Exerqtor/Voron/Firmware/rrf-macros/README.md

# Firmware Configurations

Firmware Configurations for Voron 3D printers, separated by firmware.
Remember to update this README when uploading new firmware configurations!

## Table structure

Update the following table with the information about your mod:
- Your name
- A link to your sub-folder
- A short description of your firmware config
- The printer compatibility. Use `:heavy_check_mark:` for :heavy_check_mark:,`:x:` for :x: and `:grey_question:` for :grey_question:

like so:
`
| Creator | [Config Title](link) | Description | :x: | :x: | :x: | :x: |`

---
## RepRapFirmware

| Creator | Config title | Description | V0 | V1.8 | V2.4 | VSW | VT |
| --- | --- | --- | --- | --- | --- | --- | --- |
| Exerqtor | [Adaptive Purge](./adaptive_purge/) | Purges a Voron logo right next to the print | - | - | - | - | - |
|  | [Nozzle Scrub](./nozzle_scrub/) | Script to clean your nozzle on a brush| - | - | - | - | - |
|  | [TAP Temp Control](./tap_temp_control/) | Script to make sure the nozzle is bellow 150°C when probing| - | - | - | - | - |
|  | [M48 Probe Repeatability Test](./m48_probe_repeatability_test/) | Script to test your Z probes repeatability| - | - | - | - | - |
|  | [StealthBurner LED's](./sb_leds/) | NanoLED controll for stealthburner toolhead| - | - | - | - | - |
