Exerqtor/Voron/Mods/fume_pack/pics/fancut1.png

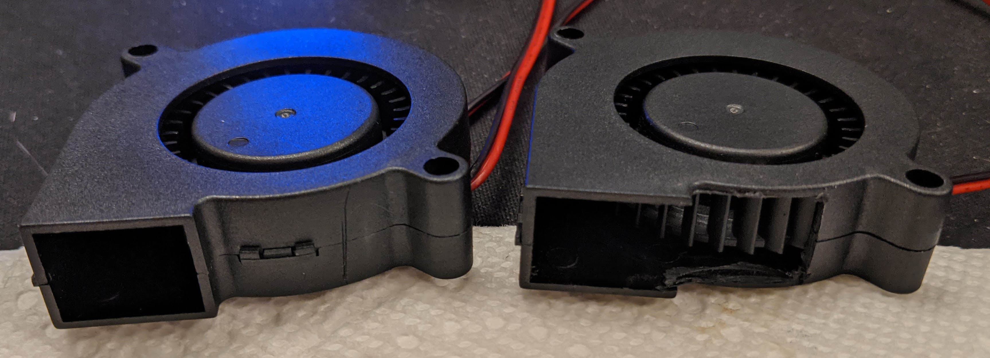
Mods/fume_pack/pics/fancut1.png
