Exerqtor/Voron/Mods/halo_hex/pics/2C-1.PNG

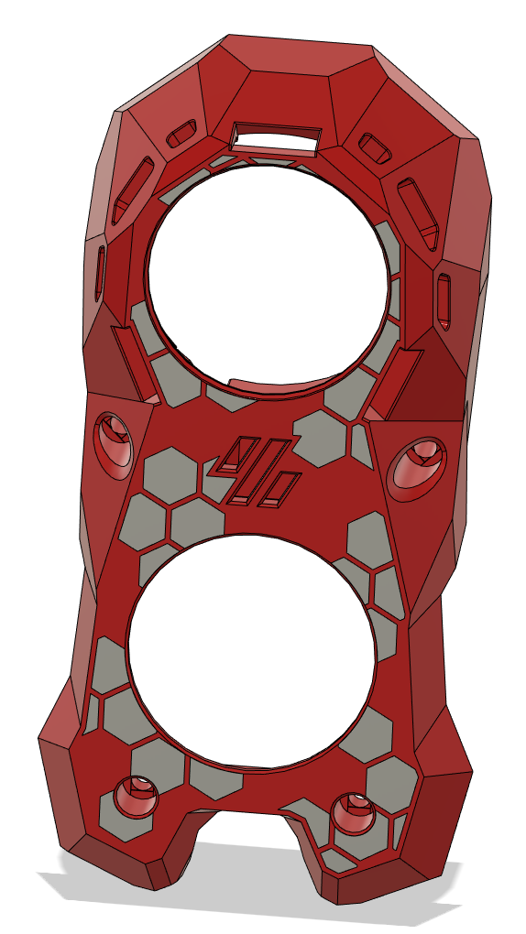
Mods/halo_hex/pics/2C-1.PNG
