Exerqtor/Voron/Mods/halo_hex/pics/3C-1.PNG

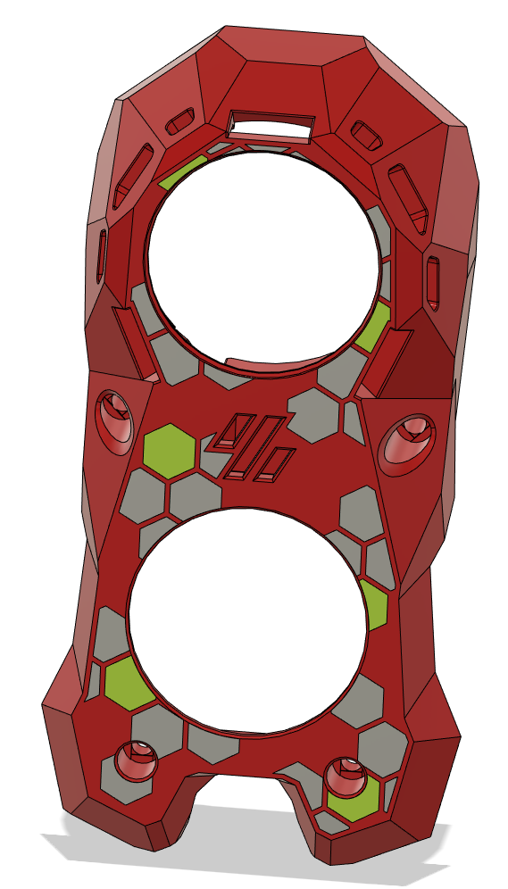
Mods/halo_hex/pics/3C-1.PNG
