Exerqtor/Voron/Mods/knomi_hex/pics/1.png

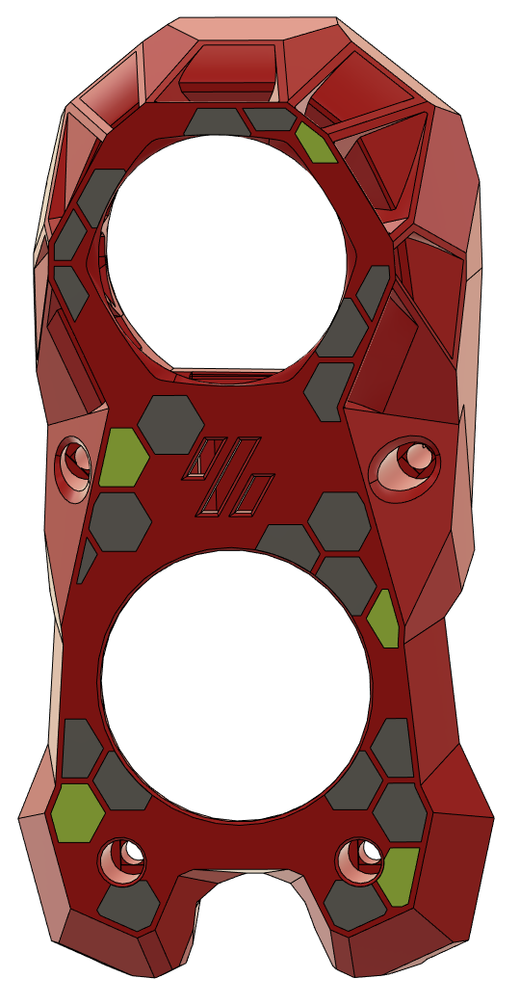
Mods/knomi_hex/pics/1.png
