Exerqtor/Voron/Mods/vt_4mm_extra_y/pics/3.PNG

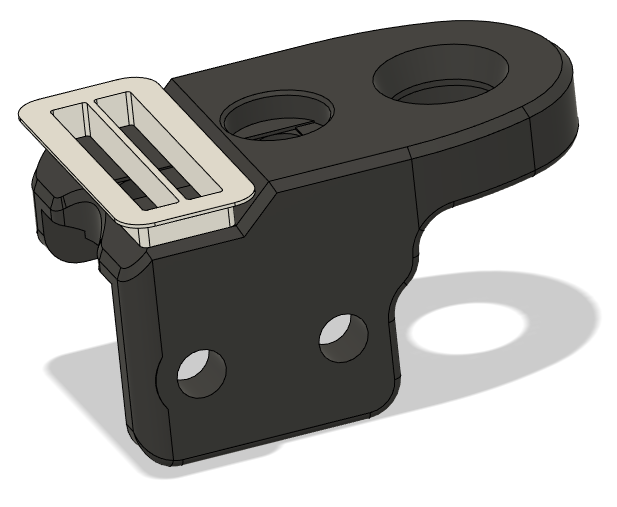
Mods/vt_4mm_extra_y/pics/3.PNG
