Exerqtor/Voron/Mods/knomi_hex/midlertidig!/NO-KNOMI-h.stl

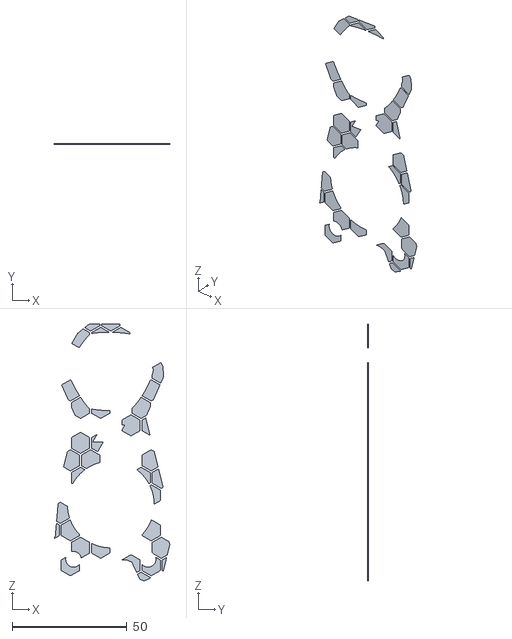
[picture p104: CAD file, 2024-03-30]
Mods/knomi_hex/midlertidig!/NO-KNOMI-h.stl
50.5 x 0.2 x 112.0
