Exerqtor/Voron/Mods/knomi_hex/STL/3_colors/KNOMI-HEX_hex-2.stl

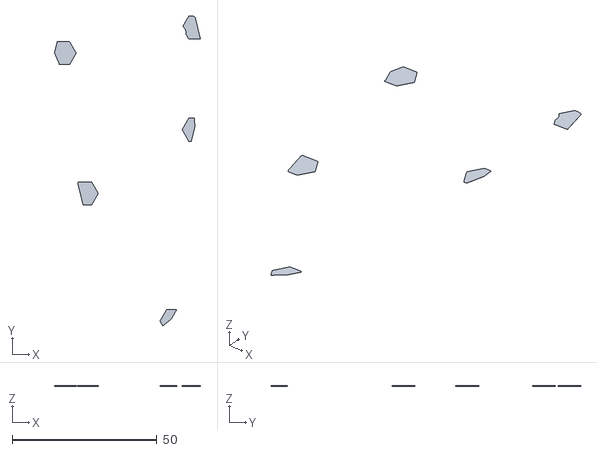
[picture p105: CAD file, 2024-03-30]
Mods/knomi_hex/STL/3_colors/KNOMI-HEX_hex-2.stl
50.4 x 106.9 x 0.2
