Exerqtor/Voron/Mods/lgx-lite_filament_sensor/CAD/LGX-lite_filament_sensor.step

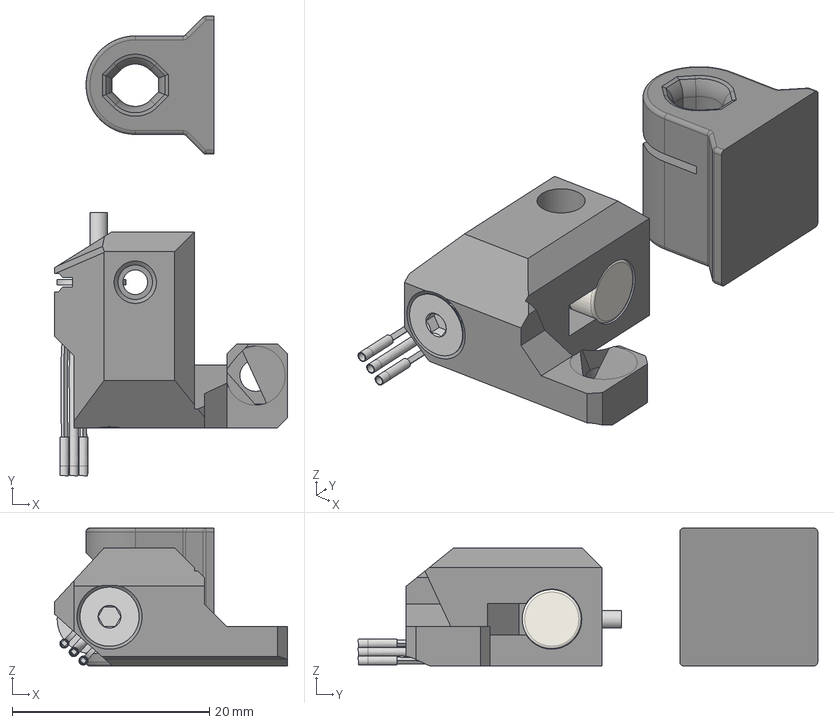
[picture p106: CAD file, 2025-02-17]
Mods/lgx-lite_filament_sensor/CAD/LGX-lite_filament_sensor.step
23.6 x 46.6 x 14.0 mm
Magnet6x3 v1
AH3364Q-P-B v4
ferromagnetic washer
92125A126_NO THREADS_18-8 Stainless Steel Hex Drive Flat Head Screw
Filament stump
PTFE cut jig
