Exerqtor/Voron/Mods/lgx-lite_filament_sensor/STL/PTFE_cut_jig.stl

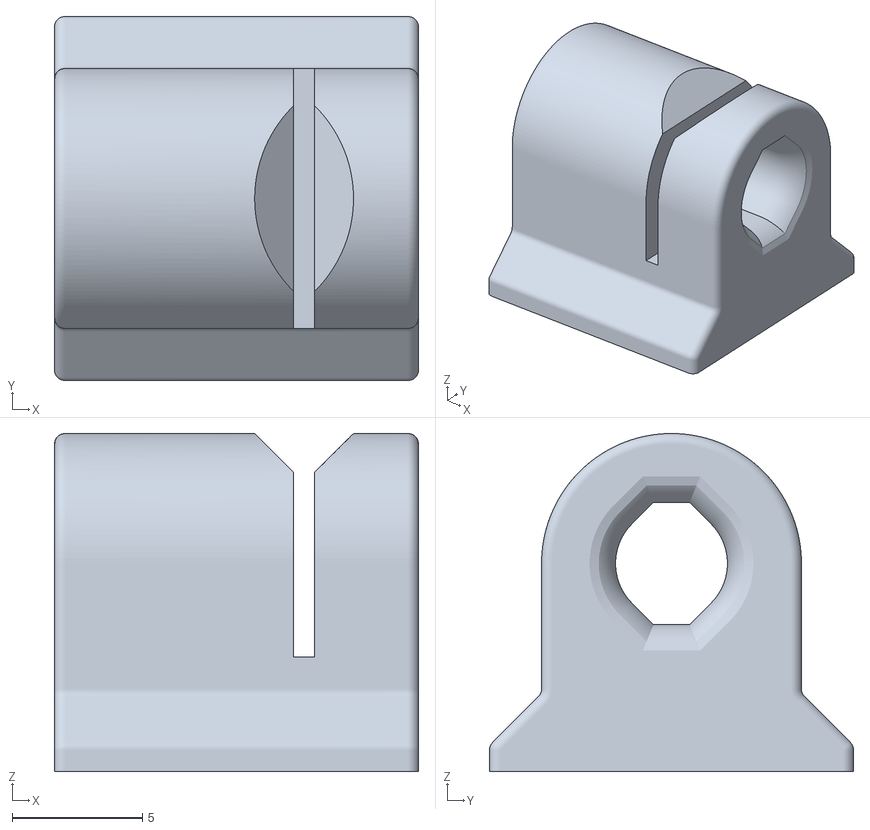
[picture p107: CAD file, 2025-02-17]
Mods/lgx-lite_filament_sensor/STL/PTFE_cut_jig.stl
14.0 x 14.0 x 13.0
