Exerqtor/Voron/Mods/mesh_skirts/Middle_Fan_Support/CAD/Middle_Fan_Support.step

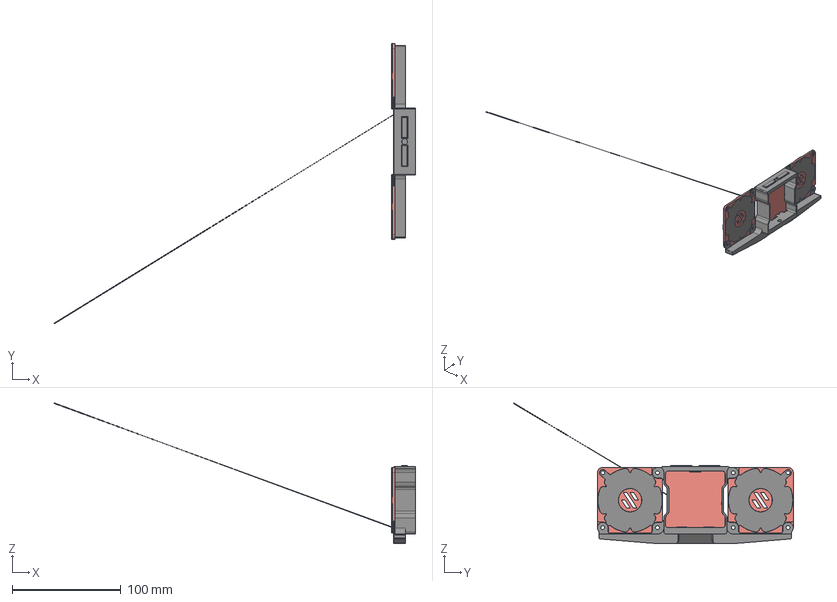
[picture p108: CAD file, 2023-04-12]
Mods/mesh_skirts/Middle_Fan_Support/CAD/Middle_Fan_Support.step
331.8 x 257.0 x 129.1 mm
Middle Fan Support
Fan Grill B
Fan Grill A
