Exerqtor/Voron/Mods/mesh_skirts/Middle_Fan_Support/STL/side_fan_support_x2.stl

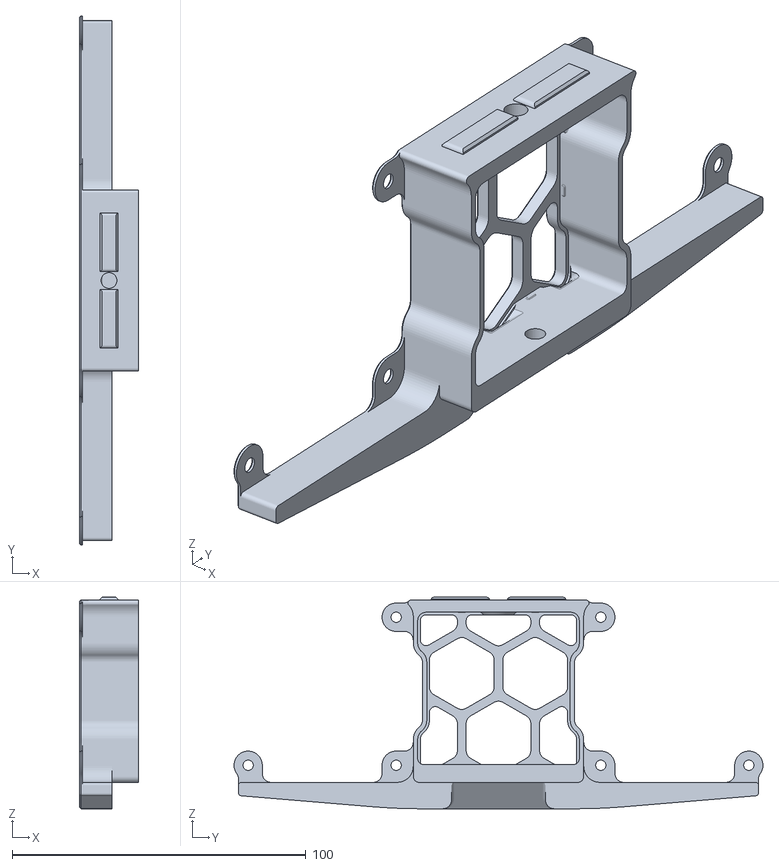
[picture p109: CAD file, 2023-04-12]
Mods/mesh_skirts/Middle_Fan_Support/STL/side_fan_support_x2.stl
20.0 x 180.0 x 72.0
