Exerqtor/Voron/Mods/mesh_skirts/V2/CAD/V2_Mesh_skirts.step

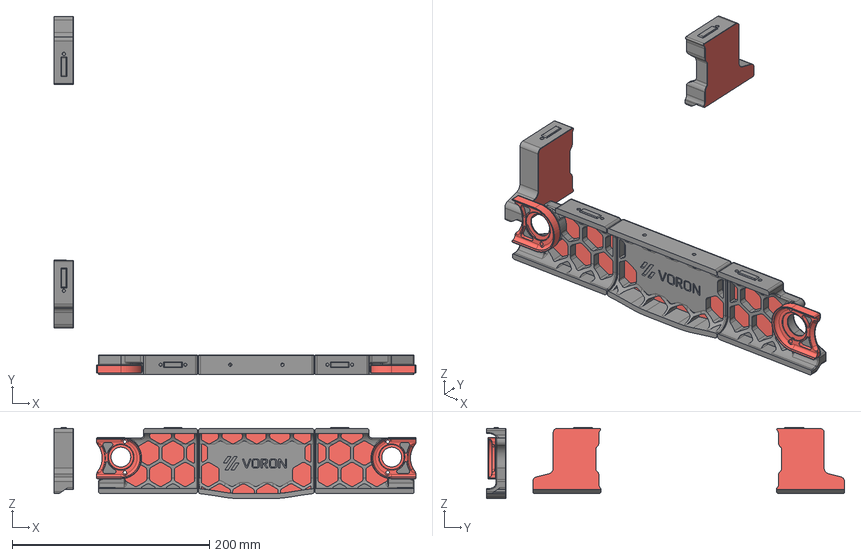
[picture p110: CAD file, 2023-04-13]
Mods/mesh_skirts/V2/CAD/V2_Mesh_skirts.step
366.8 x 363.0 x 72.0 mm
Front_Skirt_Logo
Belt_Guard (1)
Belt_Guard (2)
