Exerqtor/Voron/Mods/mesh_skirts/V2/STL/[a]_front_center_logo-mesh.stl

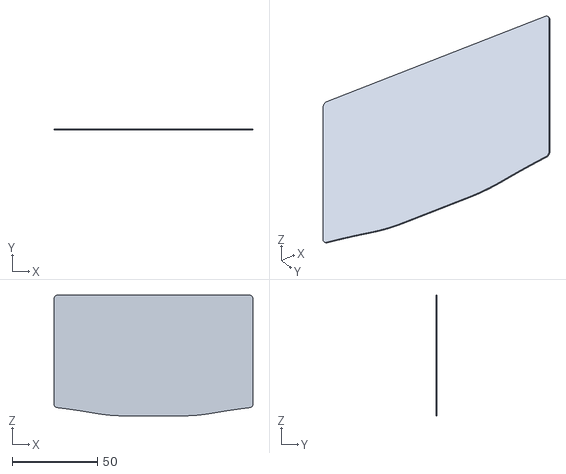
[picture p111: CAD file, 2023-04-13]
Mods/mesh_skirts/V2/STL/[a]_front_center_logo-mesh.stl
117.0 x 0.6 x 71.0
