Exerqtor/Voron/Mods/mesh_skirts/VT/STL/250/front_skirt_a_250.stl

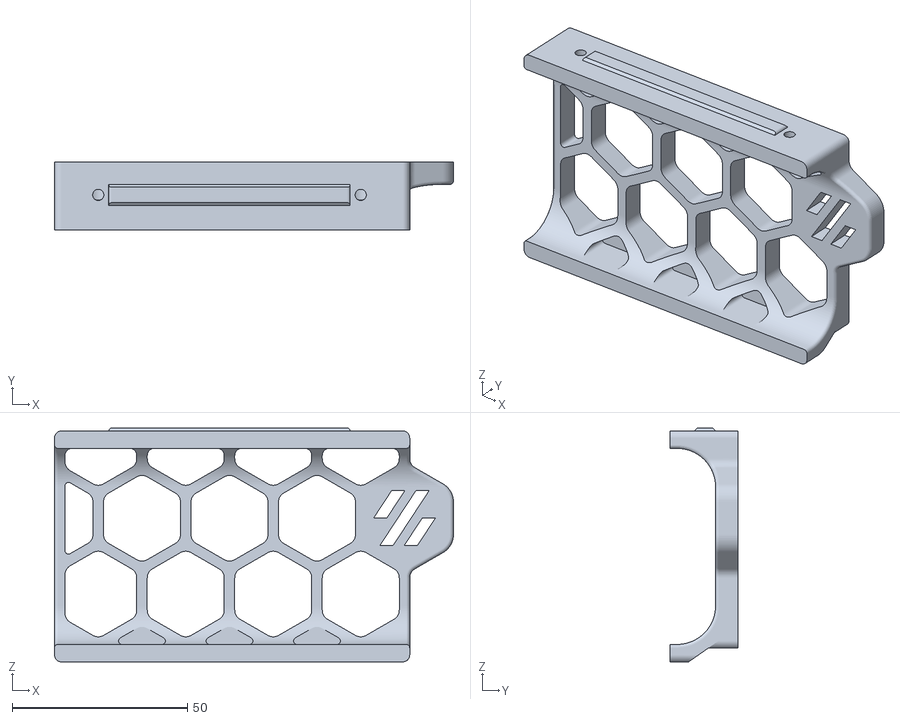
[picture p112: CAD file, 2023-04-16]
Mods/mesh_skirts/VT/STL/250/front_skirt_a_250.stl
114.0 x 19.4 x 66.8
