Exerqtor/Voron/Mods/mesh_skirts/VT/STL/350/rear_center_skirt_350.stl

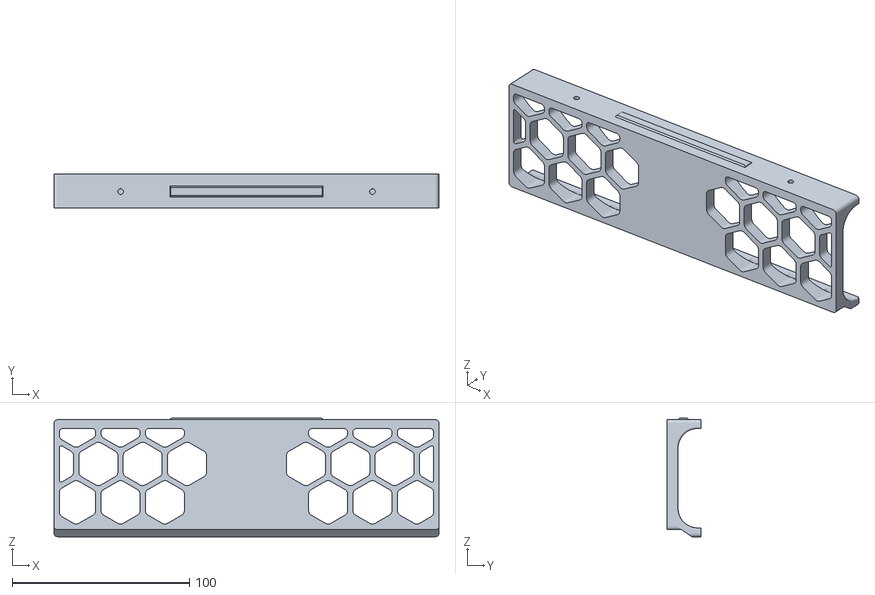
[picture p113: CAD file, 2023-04-16]
Mods/mesh_skirts/VT/STL/350/rear_center_skirt_350.stl
217.0 x 19.4 x 66.8
