Exerqtor/Voron/Mods/mgn12h_rear_z/CAD/MGN12H_Z_Carriage_Rear.step

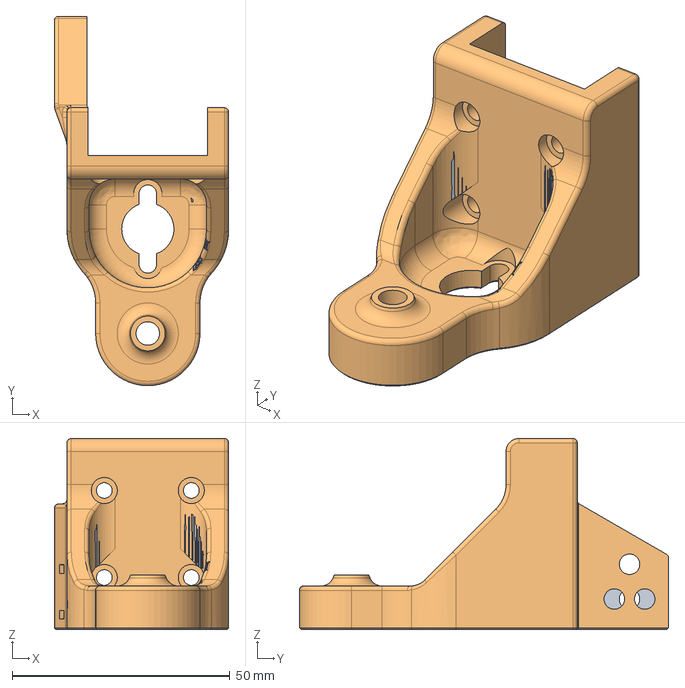
[picture p114: CAD file, 2023-04-11]
Mods/mgn12h_rear_z/CAD/MGN12H_Z_Carriage_Rear.step
40.1 x 84.9 x 43.9 mm
Z_Carriage_Rear_2-hole (IGUS)
Z_Carriage_Rear_3-hole (Generic)
