Exerqtor/Voron/Mods/mgn12h_rear_z/STL/MGN12H_Z_Carriage_Rear_2-hole-(IGUS).stl

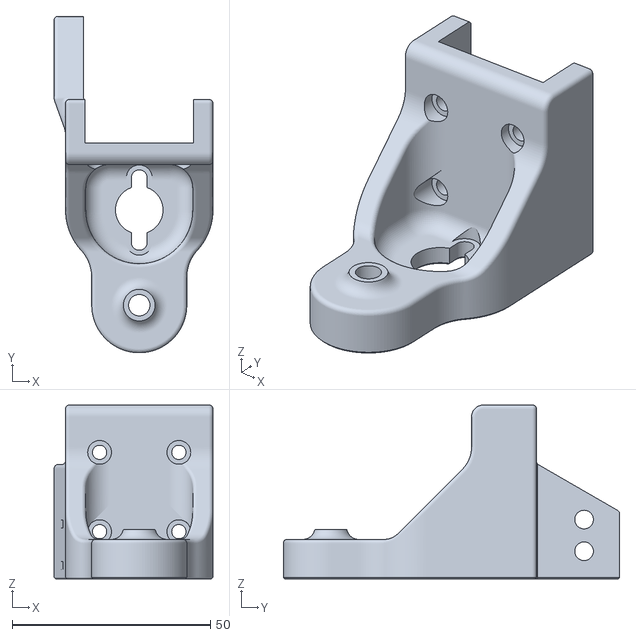
[picture p115: CAD file, 2023-04-11]
Mods/mgn12h_rear_z/STL/MGN12H_Z_Carriage_Rear_2-hole-(IGUS).stl
40.1 x 84.9 x 43.9
