Exerqtor/Voron/Mods/pepe_pack_v2/STL/Drill_template-v2.2.stl

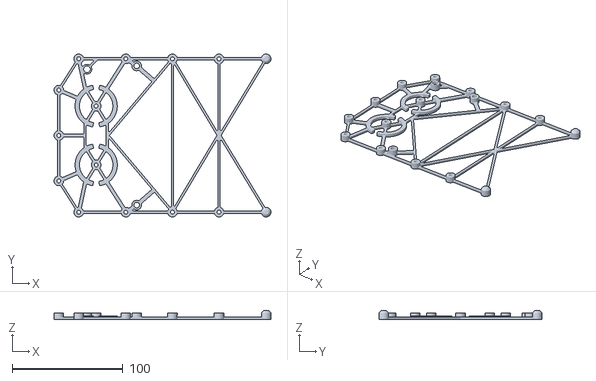
[picture p116: CAD file, 2022-12-02]
Mods/pepe_pack_v2/STL/Drill_template-v2.2.stl
195.6 x 146.9 x 8.00
