Exerqtor/Voron/Mods/quick_release_exhaust_mount/CAD/Quick_release_exhaust_mount.step

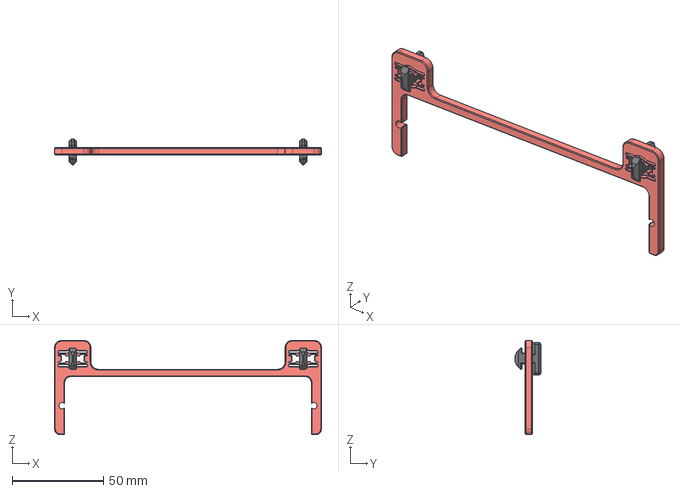
[picture p117: CAD file, 2022-11-29]
Mods/quick_release_exhaust_mount/CAD/Quick_release_exhaust_mount.step
146.4 x 14.1 x 51.6 mm
