Exerqtor/Voron/Mods/quick_release_exhaust_mount/STL/Key_x2.stl

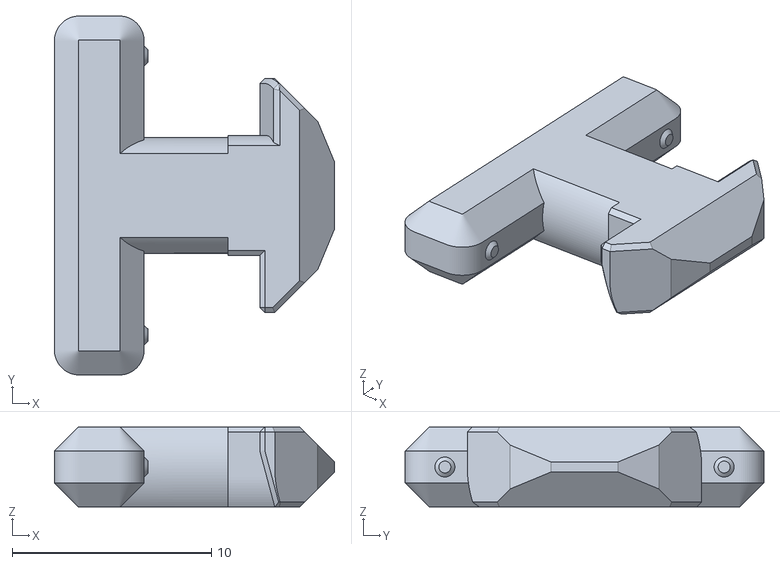
[picture p118: CAD file, 2022-11-29]
Mods/quick_release_exhaust_mount/STL/Key_x2.stl
14.1 x 18.0 x 4.00
