Exerqtor/Voron/Mods/revo_nozzle_storage_skirt/CAD/Revo_Nozzle_Storage_Skirt.step

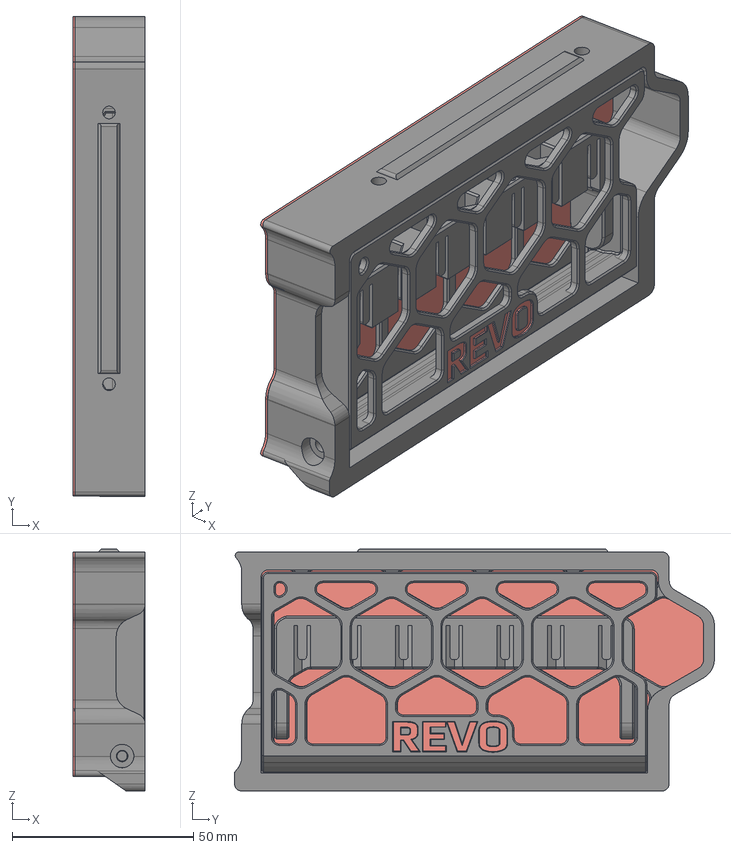
[picture p119: CAD file, 2023-04-18]
Mods/revo_nozzle_storage_skirt/CAD/Revo_Nozzle_Storage_Skirt.step
20.0 x 132.5 x 66.8 mm
Skirt
Lid
Nozzle_carrier
