Exerqtor/Voron/Mods/revo_nozzle_storage_skirt/STL/VT/350/A/[a]_MM-revo_nozzle_side_skirt_a_350-mesh.stl

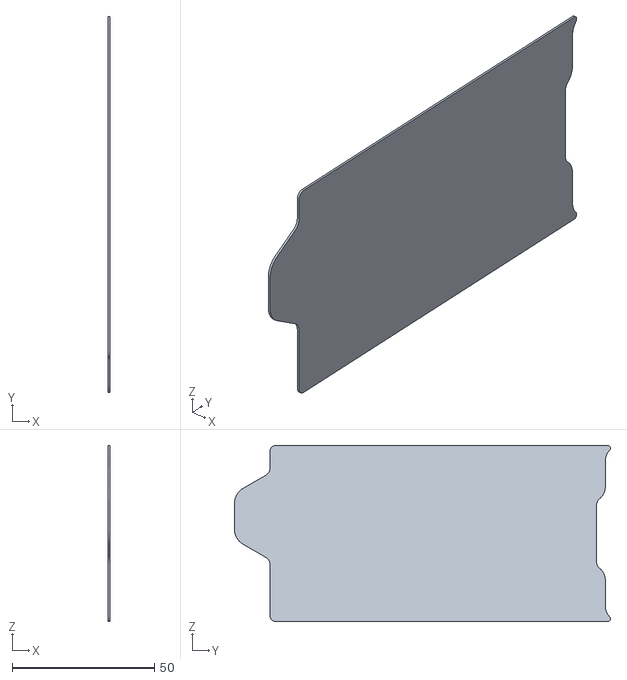
[picture p120: CAD file, 2023-06-25]
Mods/revo_nozzle_storage_skirt/STL/VT/350/A/[a]_MM-revo_nozzle_side_skirt_a_350-mesh.stl
0.6 x 132.3 x 62.0
