Exerqtor/Voron/Mods/revo_nozzle_storage_skirt/STL/VT/350/B/MM-revo_nozzle_side_skirt_b_350-brim_ears.stl

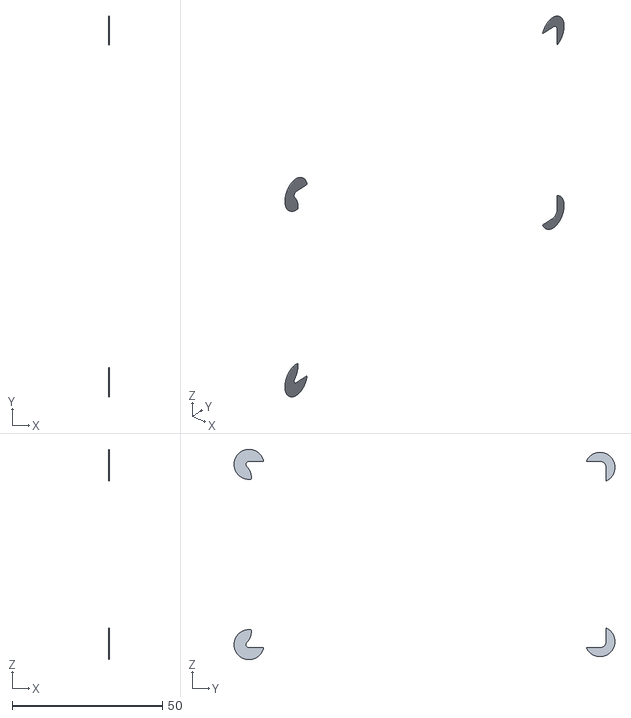
[picture p121: CAD file, 2023-06-25]
Mods/revo_nozzle_storage_skirt/STL/VT/350/B/MM-revo_nozzle_side_skirt_b_350-brim_ears.stl
0.2 x 126.8 x 70.0
