Exerqtor/Voron/Mods/revo_nozzle_storage_skirt/STL/VT/350/revo_nozzle_carrier.stl

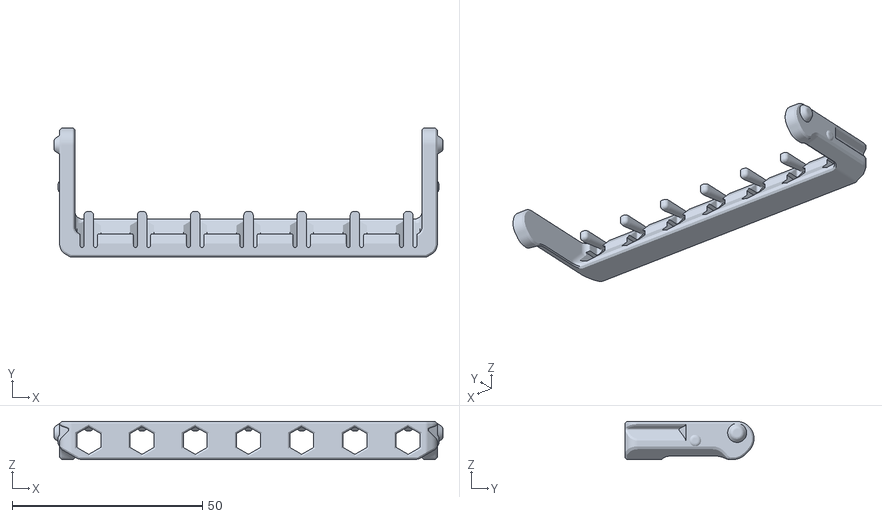
[picture p122: CAD file, 2023-06-25]
Mods/revo_nozzle_storage_skirt/STL/VT/350/revo_nozzle_carrier.stl
102.3 x 33.9 x 10.0
