Exerqtor/Voron/Mods/sensorless_tap/CAD/SENSORLESS X Carriage Center.step

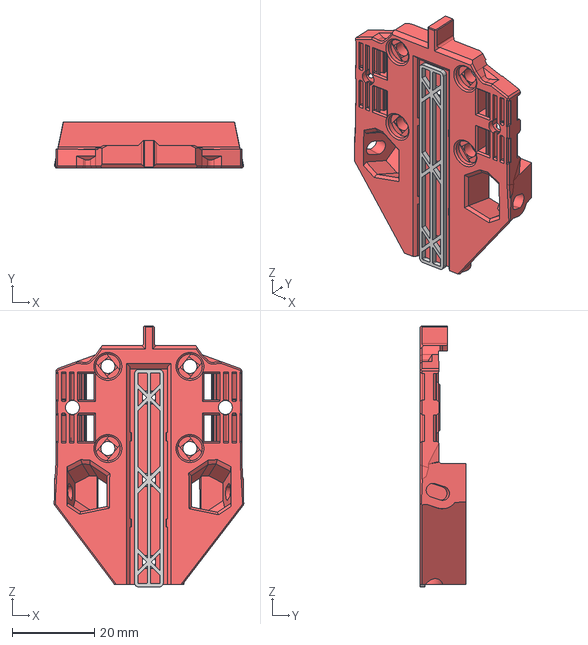
[picture p123: CAD file, 2023-05-06]
Mods/sensorless_tap/CAD/SENSORLESS X Carriage Center.step
46.2 x 11.1 x 63.6 mm
