Exerqtor/Voron/Mods/service_rockers/STL/right.stl

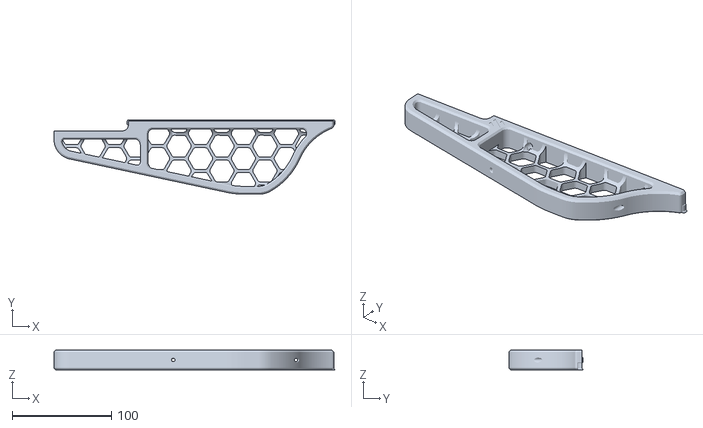
[picture p124: CAD file, 2023-05-18]
Mods/service_rockers/STL/right.stl
283.4 x 75.1 x 20.0
