Exerqtor/Voron/Mods/side_handles/CAD/Side_handles.step

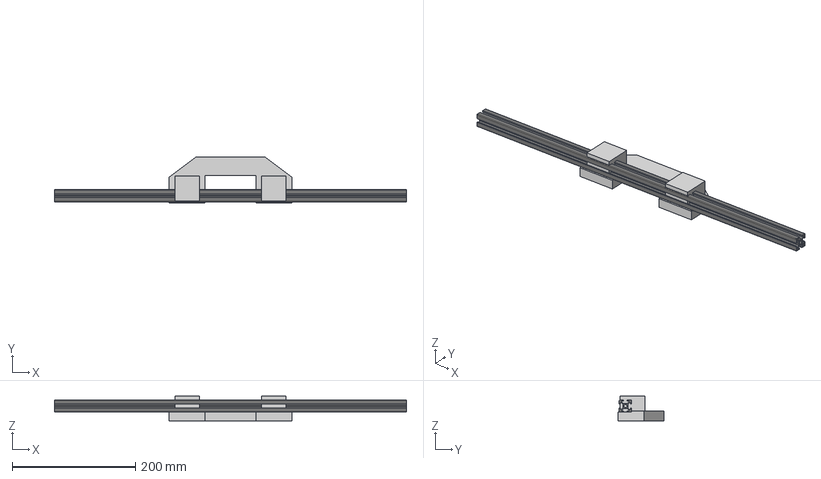
[picture p125: CAD file, 2024-03-30]
Mods/side_handles/CAD/Side_handles.step
571.2 x 75.0 x 40.0 mm
HFSB5-2020-370-TPW
Side handles
91292A123_18-8 Stainless Steel Socket Head Screw x 4
92095A212_NO THREADS x 2
