Exerqtor/Voron/Mods/side_handles/STL/[a]_Handle-X.stl

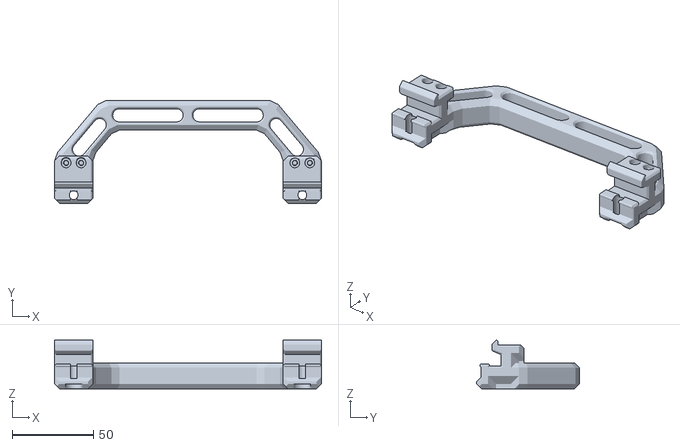
[picture p126: CAD file, 2024-03-30]
Mods/side_handles/STL/[a]_Handle-X.stl
163.8 x 63.0 x 29.9
