Exerqtor/Voron/Mods/side_handles/STL/modifiers/Infill.stl

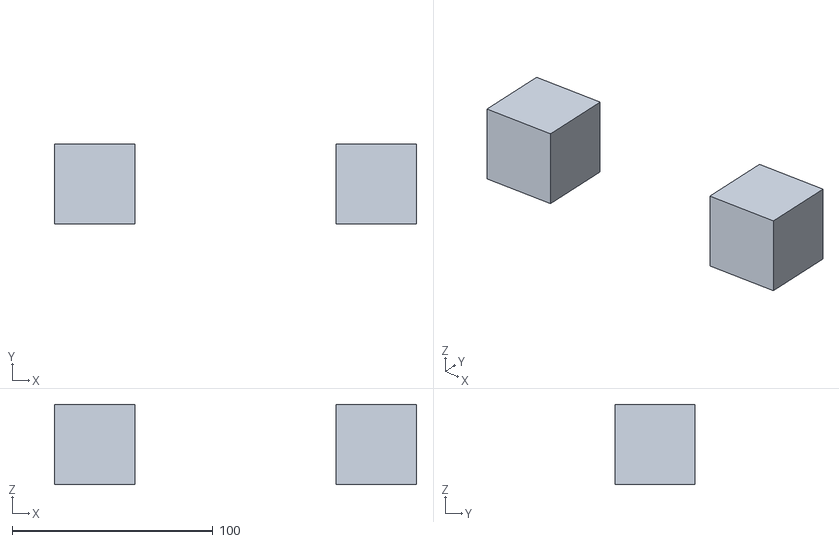
[picture p127: CAD file, 2024-03-30]
Mods/side_handles/STL/modifiers/Infill.stl
180.3 x 40.0 x 40.0
