Exerqtor/Voron/Mods/stealthburner_cw2_style_lgx_lite_mount/CAD/LGX Lite SB ERCF OPEN.step

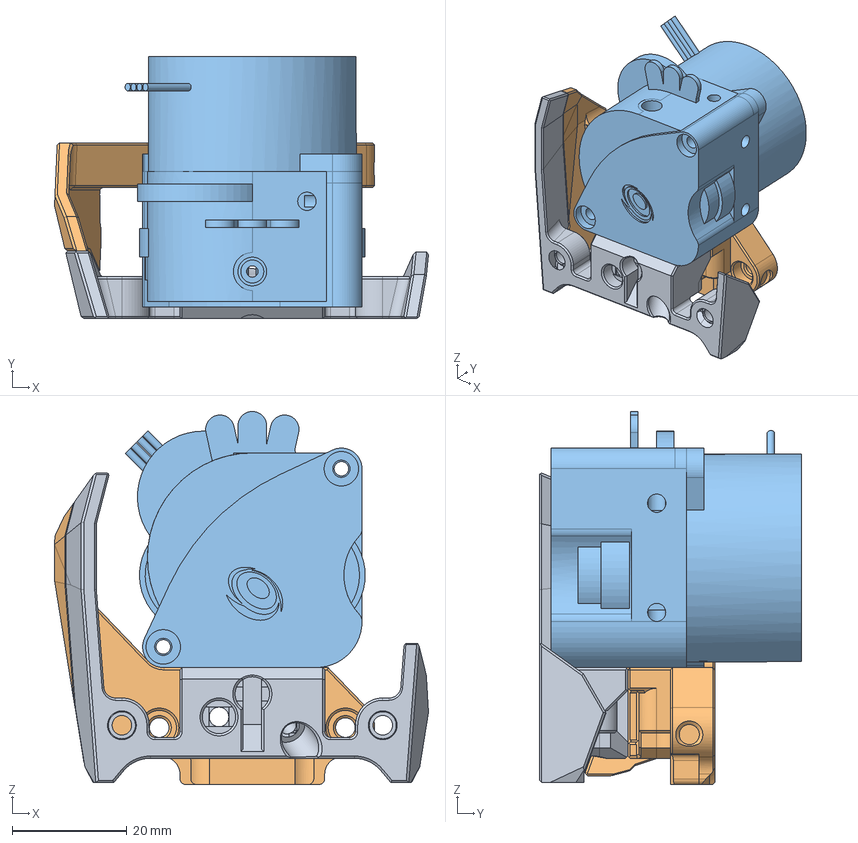
[picture p128: CAD file, 2023-05-08]
Mods/stealthburner_cw2_style_lgx_lite_mount/CAD/LGX Lite SB ERCF OPEN.step
65.1 x 45.6 x 64.9 mm
Front_body_LGX_Lite_Stealthburner_ERCF_Released_rev01
Rear_body_LGX_Lite_Stealthburner_ERCF_Released_rev01
LGX-Lite Dummy
