Exerqtor/Voron/Mods/stealthburner_cw2_style_lgx_lite_mount/STL/OPEN-front_body_lgx_lite_sb_erfc.stl

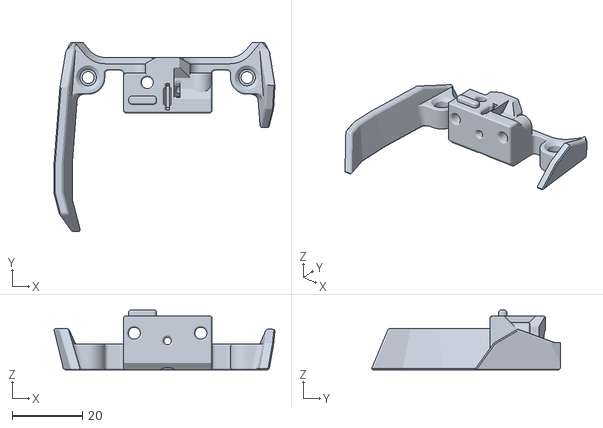
[picture p129: CAD file, 2023-05-08]
Mods/stealthburner_cw2_style_lgx_lite_mount/STL/OPEN-front_body_lgx_lite_sb_erfc.stl
63.1 x 53.9 x 17.0
