Exerqtor/Voron/Mods/trident_ptfe_guides/CAD/Trident_PTFE_guides-R40.step

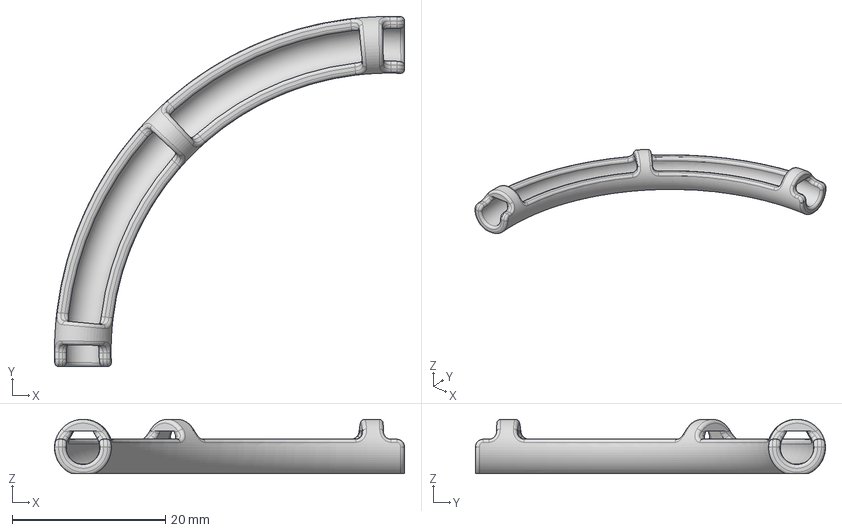
[picture p130: CAD file, 2023-09-23]
Mods/trident_ptfe_guides/CAD/Trident_PTFE_guides-R40.step
45.7 x 45.7 x 7.10 mm
