Exerqtor/Voron/Mods/trident_ptfe_guides/STL/R40-105°.stl

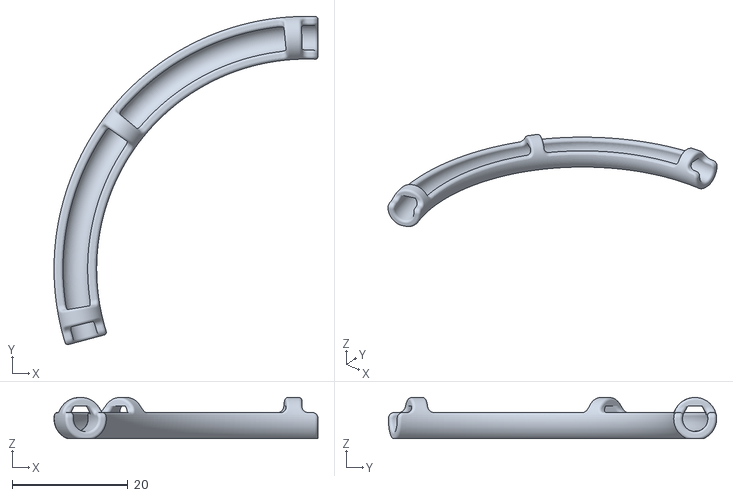
[picture p131: CAD file, 2023-09-23]
Mods/trident_ptfe_guides/STL/R40-105°.stl
45.7 x 56.8 x 7.10
