Exerqtor/Voron/Mods/trident_ptfe_support-v2/CAD/Trident_PTFE_support-v2.step

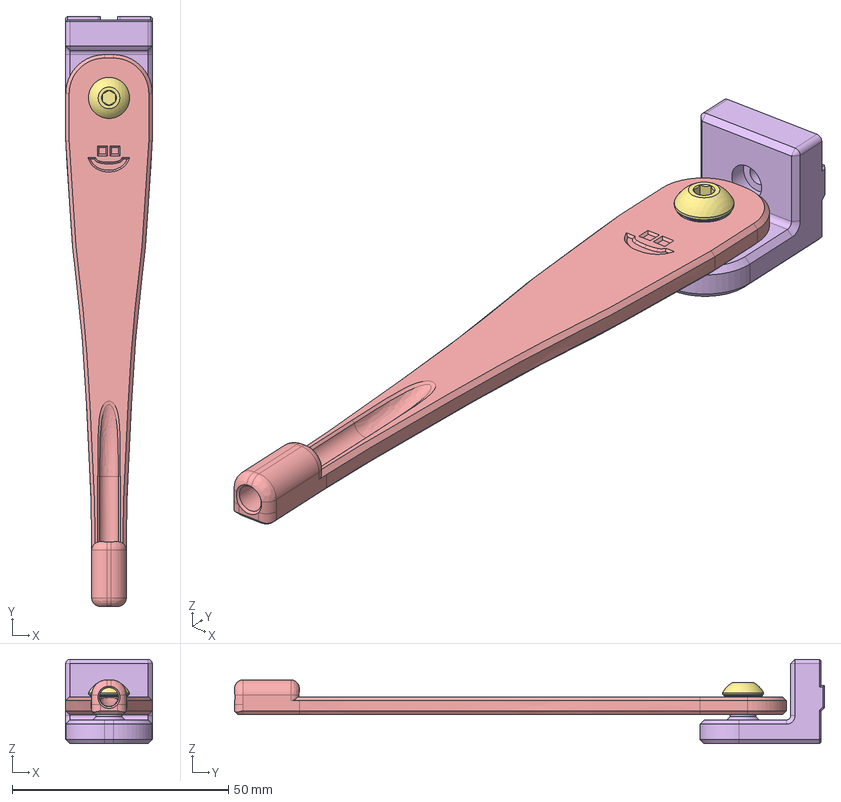
[picture p132: CAD file, 2022-11-29]
Mods/trident_ptfe_support-v2/CAD/Trident_PTFE_support-v2.step
20.0 x 136.3 x 19.5 mm
MR85 Bearing
Mount
M3x10 BHCS
Spacer
