Exerqtor/Voron/Mods/trident_ptfe_support-v2/STL/Spacer.stl

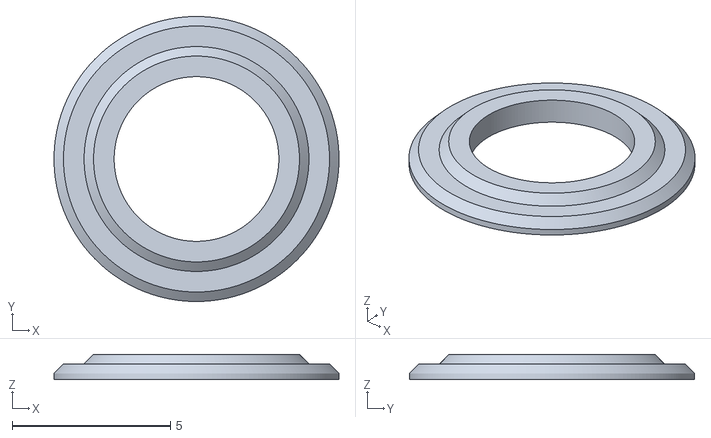
[picture p133: CAD file, 2022-11-29]
Mods/trident_ptfe_support-v2/STL/Spacer.stl
9.00 x 9.00 x 0.8
