Exerqtor/Voron/Mods/vt_4mm_extra_y/STL/4mm_ Extra_Y-travel_rear-v7.stl

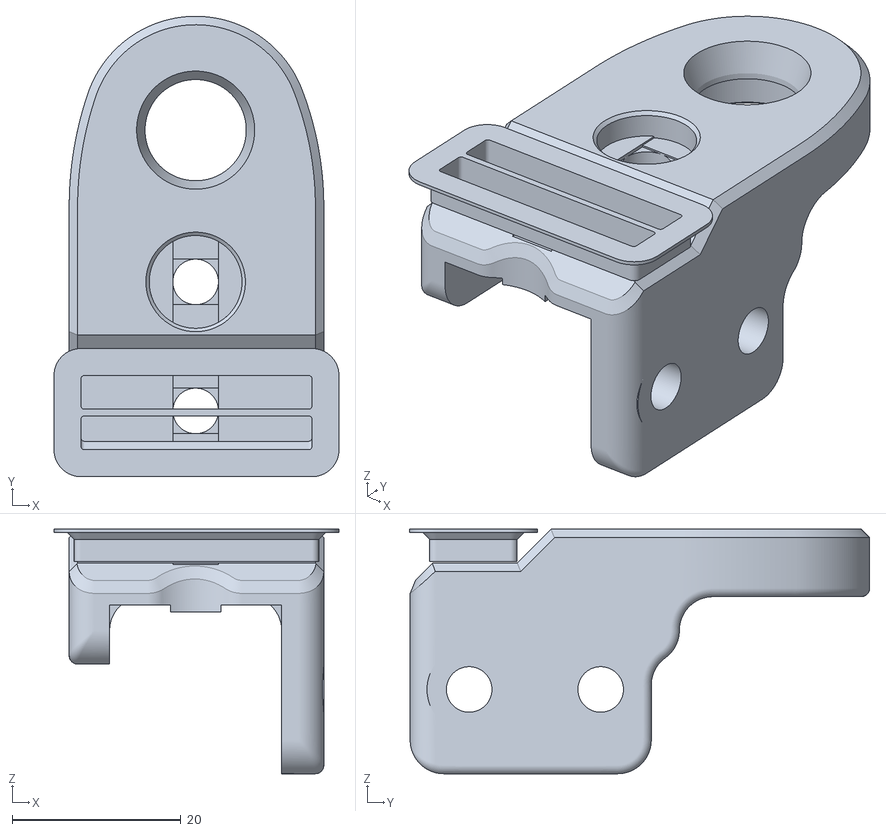
[picture p134: CAD file, 2023-04-29]
Mods/vt_4mm_extra_y/STL/4mm_ Extra_Y-travel_rear-v7.stl
33.8 x 54.6 x 29.0
