Exerqtor/Voron/Mods/vt_front_wobblex_carriers/CAD/VT Front Wobblex Carriers.step

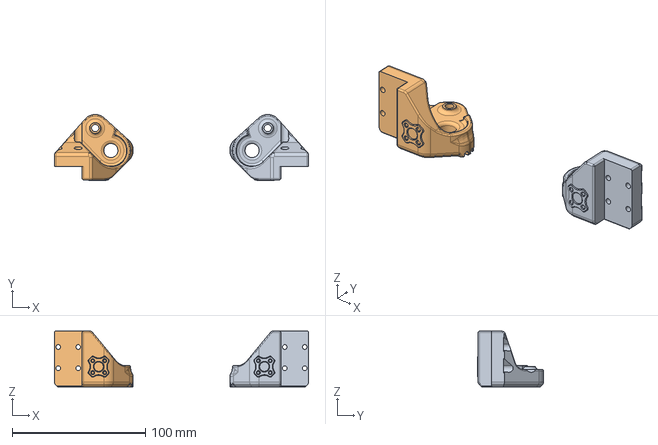
[picture p135: CAD file, 2023-04-23]
Mods/vt_front_wobblex_carriers/CAD/VT Front Wobblex Carriers.step
190.6 x 49.5 x 41.9 mm
Right
Left
