Exerqtor/Voron/Mods/vt_lowered_Z_motor_mounts/CAD/VT_Lowered_Z_Motor_Mounts-v1.1.step

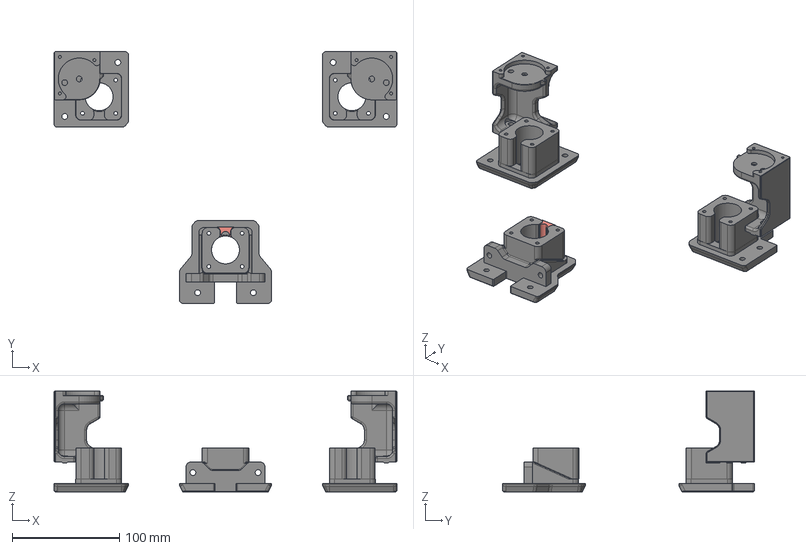
[picture p136: CAD file, 2022-12-02]
Mods/vt_lowered_Z_motor_mounts/CAD/VT_Lowered_Z_Motor_Mounts-v1.1.step
320.0 x 234.9 x 94.0 mm
Z_Motor_Mount_Left
Z_Motor_Mount_Rear
Z_Motor_Mount_Right
Cover
Corner_A
Corner_B
