Exerqtor/Voron/Mods/vt_lowered_Z_motor_mounts/STL/Z_Motor_Mount_Right-v1.1.stl

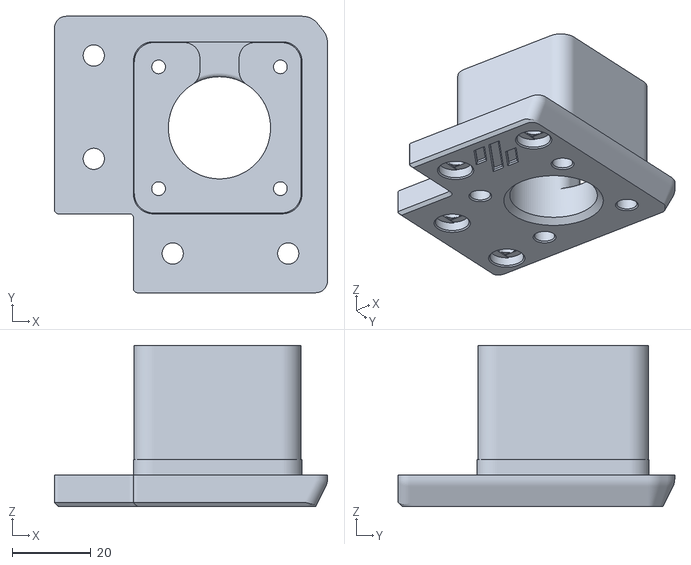
[picture p137: CAD file, 2022-12-02]
Mods/vt_lowered_Z_motor_mounts/STL/Z_Motor_Mount_Right-v1.1.stl
69.5 x 70.4 x 41.0
