Exerqtor/Voron/Mods/vt_wobblex_carriers/CAD/Top supports.step

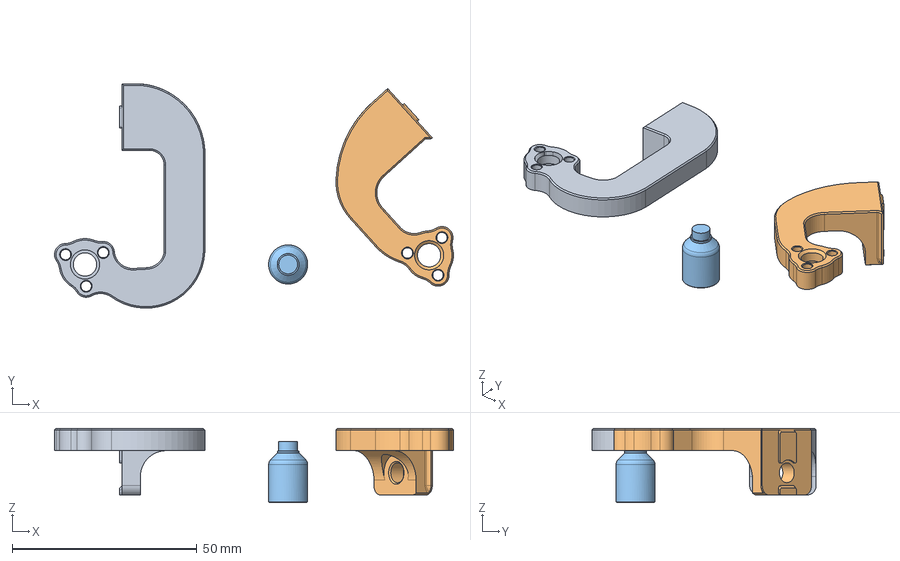
[picture p138: CAD file, 2023-08-07]
Mods/vt_wobblex_carriers/CAD/Top supports.step
108.0 x 60.7 x 20.0 mm
