Exerqtor/Voron/Mods/vt_wobblex_carriers/STL/2.9mm/WobbleX_2.9mm_z_carriage_right.stl

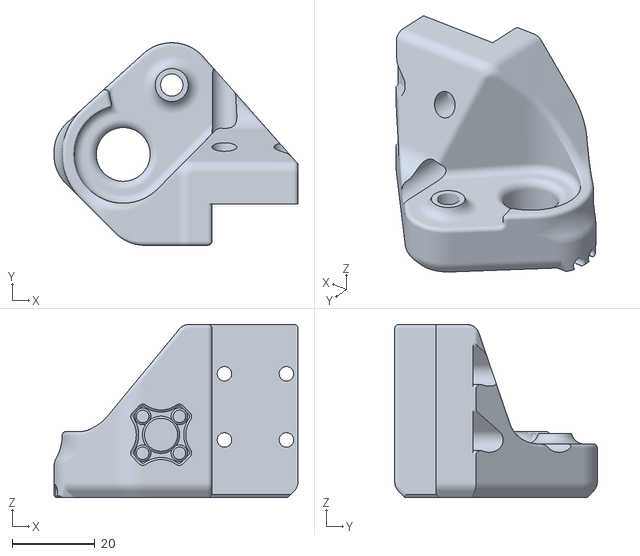
[picture p139: CAD file, 2023-08-07]
Mods/vt_wobblex_carriers/STL/2.9mm/WobbleX_2.9mm_z_carriage_right.stl
59.1 x 49.0 x 41.9
