Exerqtor/Voron/Mods/canopy_ptfe_passthrough/STL/250.stl

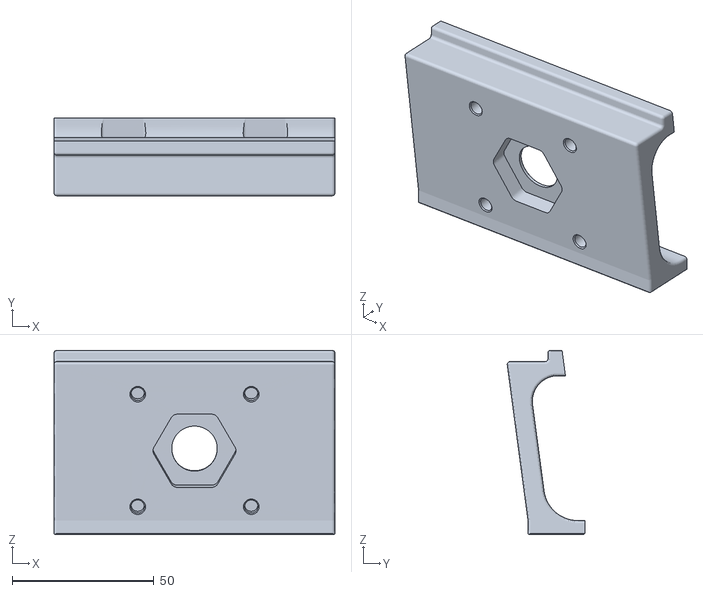
[picture p140: CAD file, 2024-03-30]
Mods/canopy_ptfe_passthrough/STL/250.stl
99.0 x 27.3 x 65.0
