Exerqtor/Voron/Mods/canopy_ptfe_passthrough/STL/ptfe-tube_support/[a]_Spacer.stl

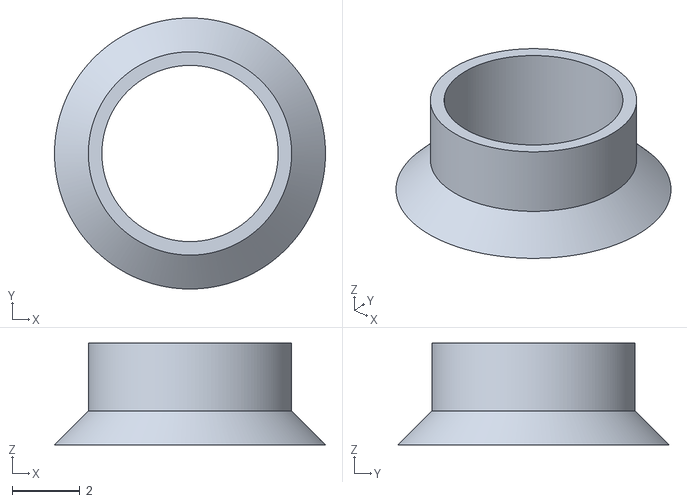
[picture p141: CAD file, 2024-03-30]
Mods/canopy_ptfe_passthrough/STL/ptfe-tube_support/[a]_Spacer.stl
8.00 x 8.00 x 3.00
