Exerqtor/Voron/Mods/fume_pack/DXF/250mm.dxf

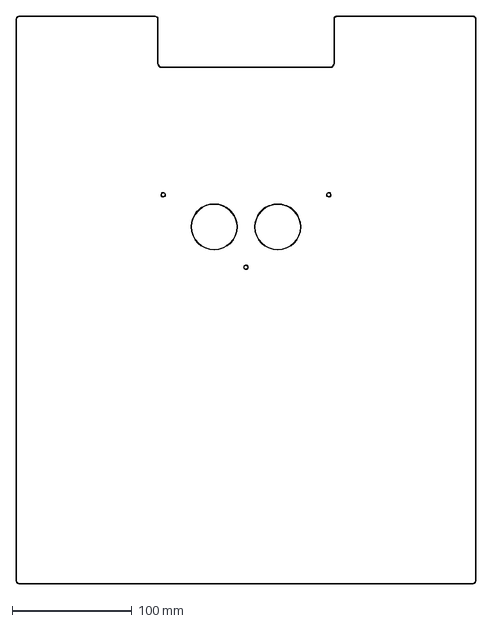
[picture p142: CAD file, 2023-06-20]
Mods/fume_pack/DXF/250mm.dxf
383.0 x 473.0 mm
