Exerqtor/Voron/Mods/fume_pack/DXFs/V2-300mm.dxf

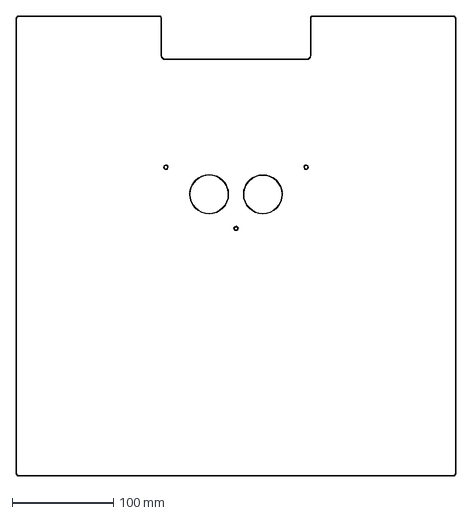
[picture p143: CAD file, 2023-06-24]
Mods/fume_pack/DXFs/V2-300mm.dxf
433.0 x 453.0 mm
