Exerqtor/Voron/Mods/halo_hex/STL/3_colors/HALO-HEX_3_colors-2.stl

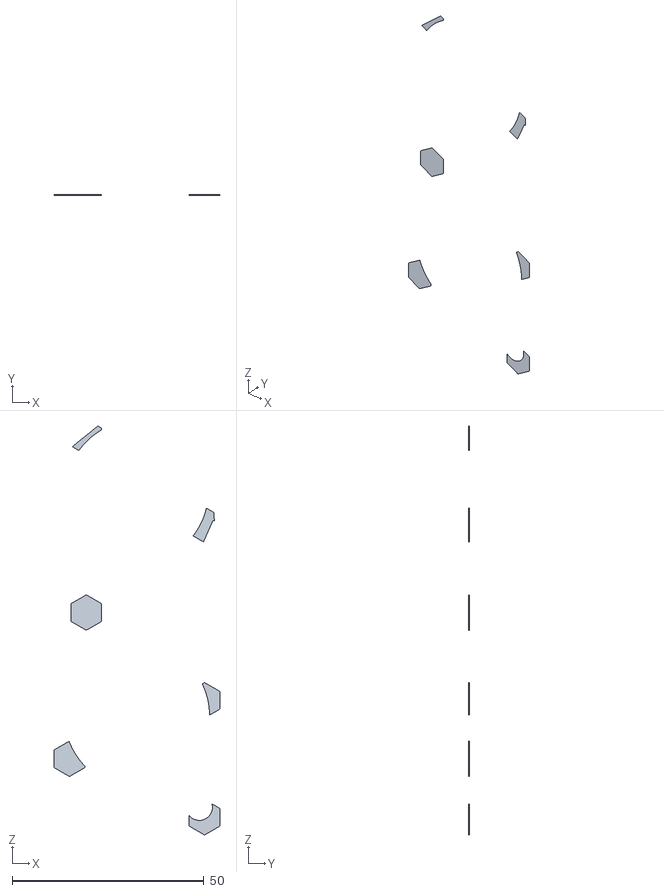
[picture p144: CAD file, 2024-03-30]
Mods/halo_hex/STL/3_colors/HALO-HEX_3_colors-2.stl
43.2 x 0.2 x 106.6
