Exerqtor/Voron/Mods/knomi_hex/STL/3_colors/KNOMI-HEX_hex-1.stl

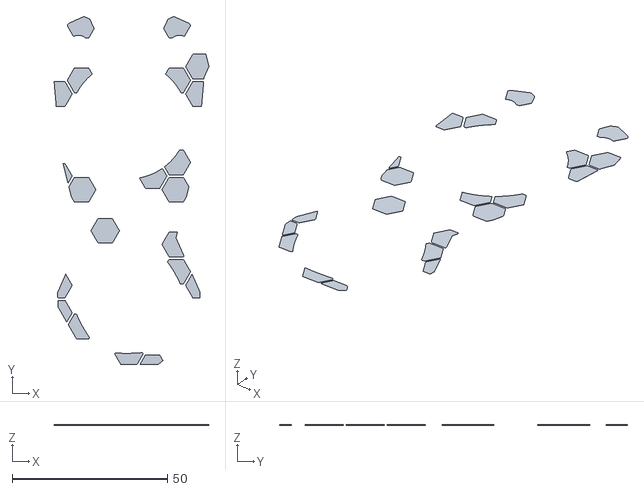
[picture p145: CAD file, 2024-03-30]
Mods/knomi_hex/STL/3_colors/KNOMI-HEX_hex-1.stl
49.8 x 112.0 x 0.2
