Exerqtor/Voron/Mods/mesh_skirts/Middle_Fan_Support/STL/[a]_fan_grill_b_x2.stl

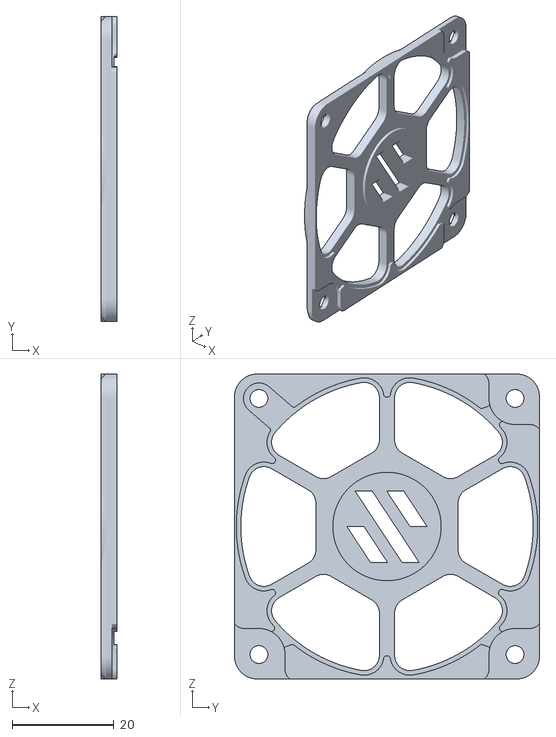
[picture p146: CAD file, 2023-04-12]
Mods/mesh_skirts/Middle_Fan_Support/STL/[a]_fan_grill_b_x2.stl
3.20 x 60.0 x 60.0
