Exerqtor/Voron/Mods/mesh_skirts/V2/STL/[a]_belt_guard_a_x2.stl

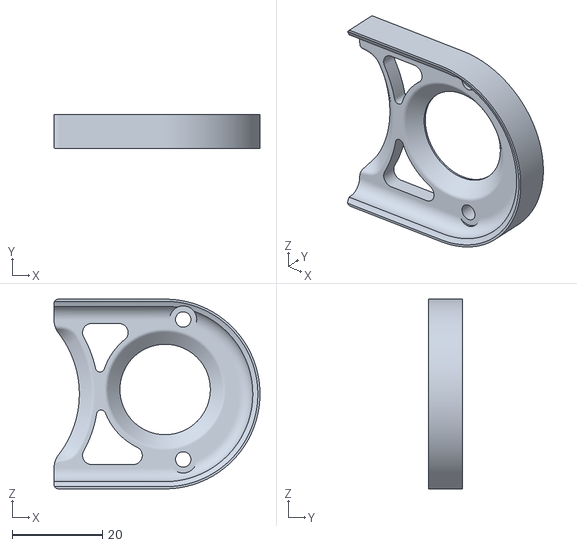
[picture p147: CAD file, 2023-04-13]
Mods/mesh_skirts/V2/STL/[a]_belt_guard_a_x2.stl
45.6 x 7.60 x 42.0
