Exerqtor/Voron/Mods/mesh_skirts/VT/STL/300/[a]_rear_center_skirt_300-mesh.stl

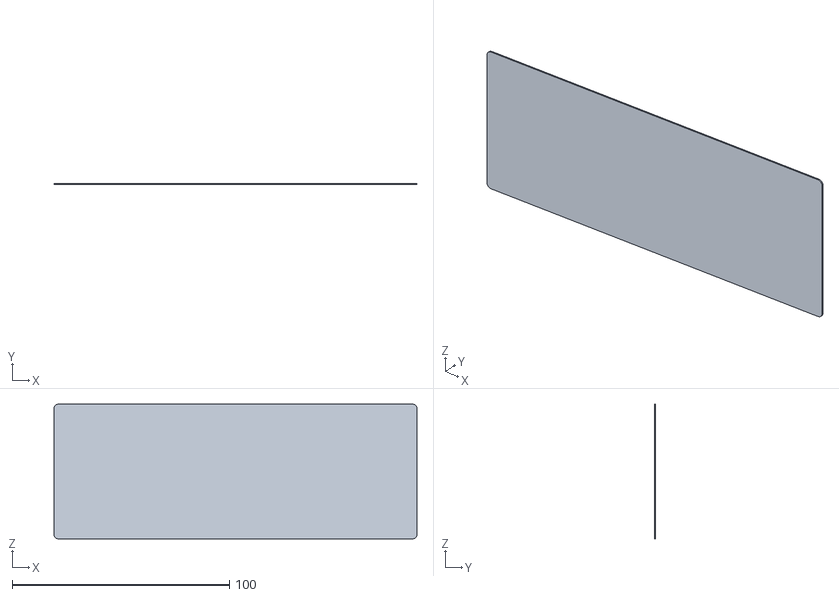
[picture p148: CAD file, 2023-04-16]
Mods/mesh_skirts/VT/STL/300/[a]_rear_center_skirt_300-mesh.stl
167.0 x 0.6 x 62.0
