Exerqtor/Voron/Mods/mesh_skirts/VT/STL/power_inlet_adamstech.stl

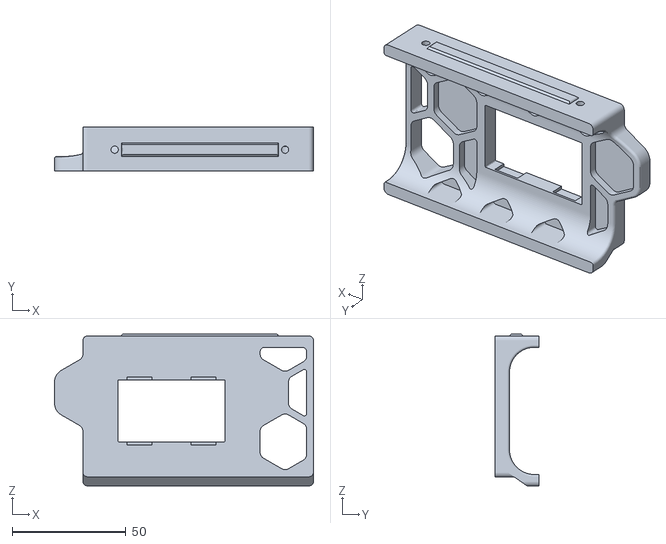
[picture p149: CAD file, 2023-04-22]
Mods/mesh_skirts/VT/STL/power_inlet_adamstech.stl
114.0 x 19.4 x 66.8
