Exerqtor/Voron/Mods/pepe_pack_v2/STL/[a]_Fan_cover-v2.2.stl

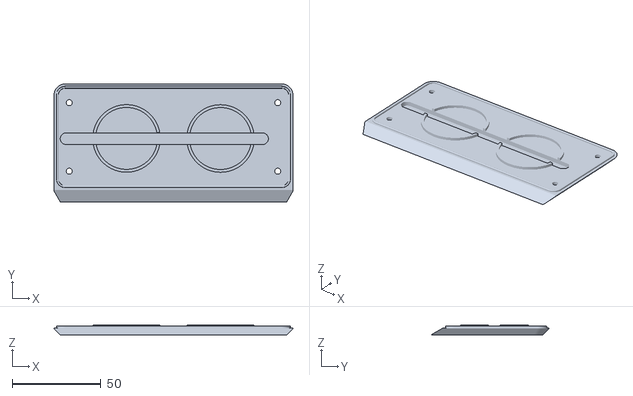
[picture p150: CAD file, 2022-11-28]
Mods/pepe_pack_v2/STL/[a]_Fan_cover-v2.2.stl
134.8 x 66.7 x 5.60
