Exerqtor/Voron/Mods/revo_nozzle_storage_skirt/STL/VT/350/A/[a]_MM-revo_nozzle_side_skirt_a_350-lid_logo.stl

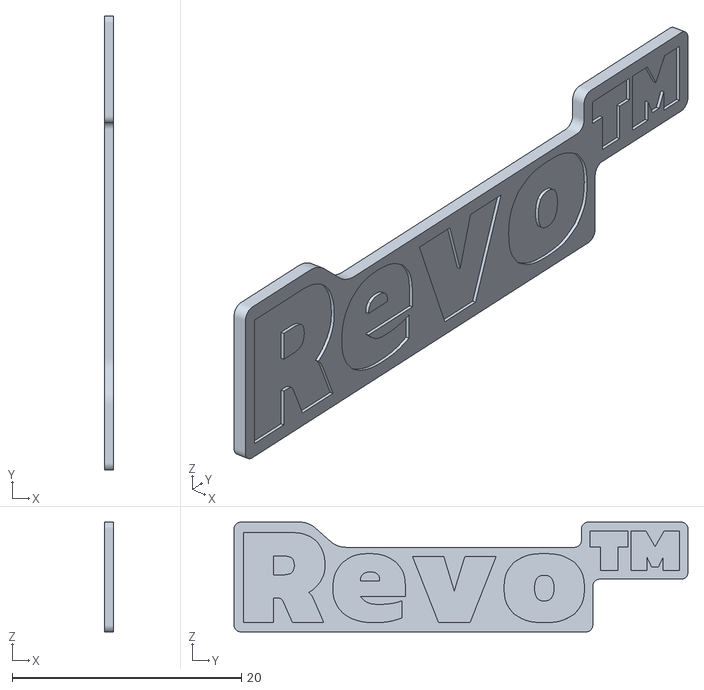
[picture p151: CAD file, 2023-06-25]
Mods/revo_nozzle_storage_skirt/STL/VT/350/A/[a]_MM-revo_nozzle_side_skirt_a_350-lid_logo.stl
0.8 x 39.6 x 9.59
