Exerqtor/Voron/Mods/revo_nozzle_storage_skirt/STL/VT/350/B/MM-revo_nozzle_side_skirt_b_350.stl

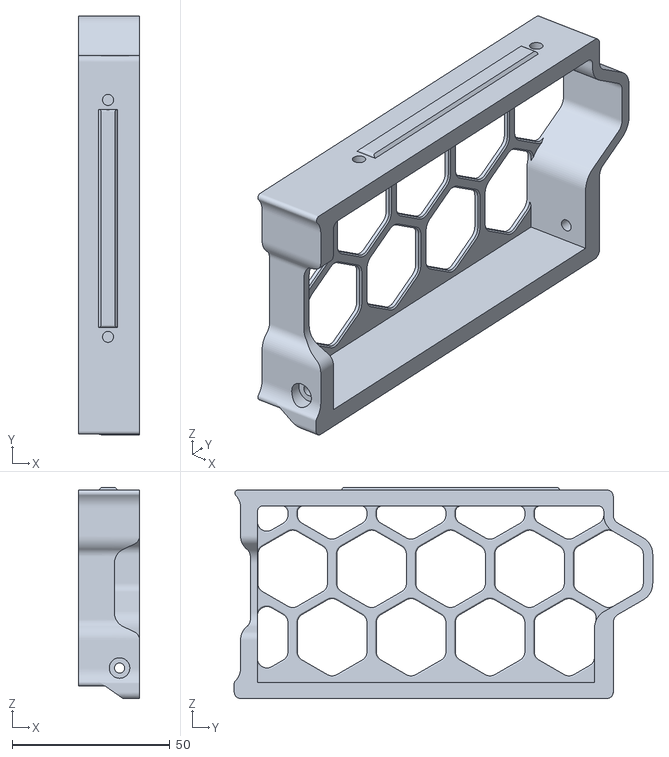
[picture p152: CAD file, 2023-06-25]
Mods/revo_nozzle_storage_skirt/STL/VT/350/B/MM-revo_nozzle_side_skirt_b_350.stl
19.4 x 132.5 x 66.8
