Exerqtor/Voron/Mods/side_handles/STL/modifiers/Fuzz.stl

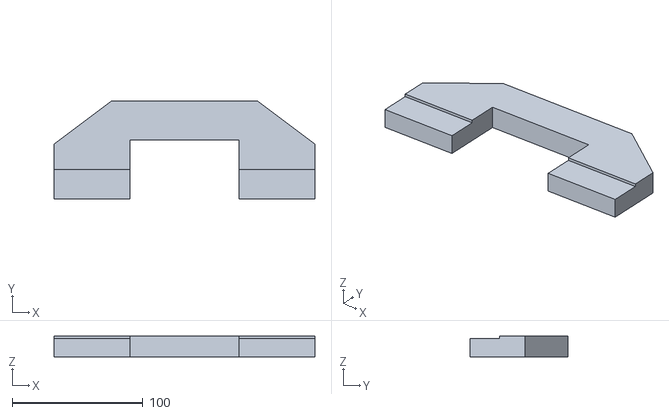
[picture p153: CAD file, 2024-03-30]
Mods/side_handles/STL/modifiers/Fuzz.stl
199.3 x 75.0 x 16.0
