Exerqtor/Voron/Mods/stealthburner_cw2_style_lgx_lite_mount/STL/OPEN-rear_body_lgx_lite_sb_ercf.stl

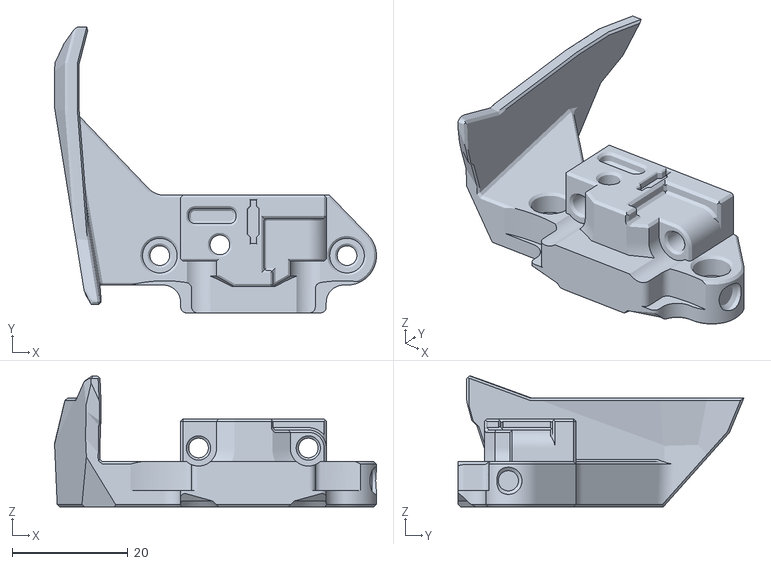
[picture p154: CAD file, 2023-05-08]
Mods/stealthburner_cw2_style_lgx_lite_mount/STL/OPEN-rear_body_lgx_lite_sb_ercf.stl
55.7 x 49.5 x 22.6
