Exerqtor/Voron/Mods/trident_ptfe_guides/CAD/Trident_PTFE_guides-R50.step

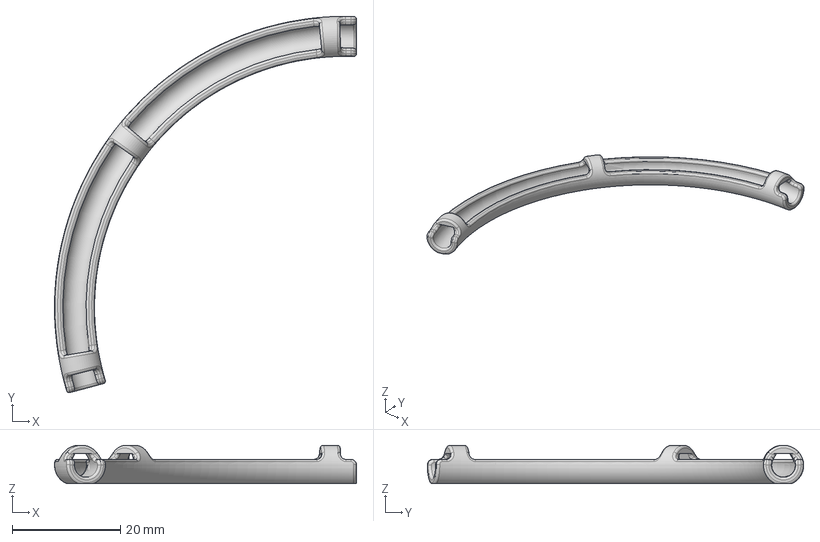
[picture p155: CAD file, 2022-11-30]
Mods/trident_ptfe_guides/CAD/Trident_PTFE_guides-R50.step
55.7 x 69.4 x 7.10 mm
