Exerqtor/Voron/Mods/vt_4mm_extra_y/STL/4mm_ Extra_Y-travel_right-v9.stl

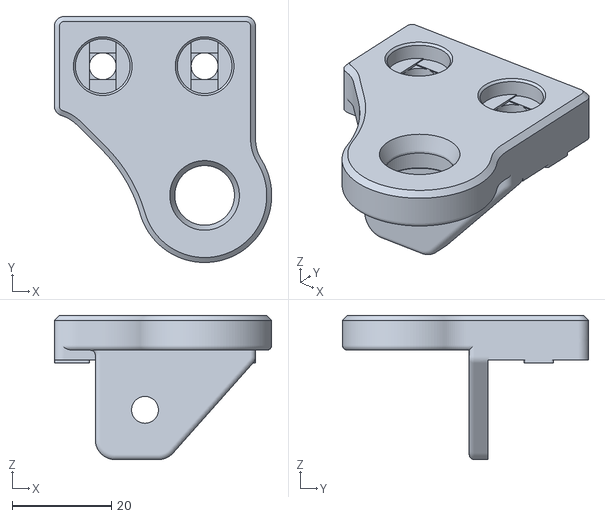
[picture p157: CAD file, 2023-04-29]
Mods/vt_4mm_extra_y/STL/4mm_ Extra_Y-travel_right-v9.stl
43.7 x 49.5 x 29.0
