Exerqtor/Voron/Mods/vt_lowered_Z_motor_mounts/STL/Corner_B-v1.1.stl

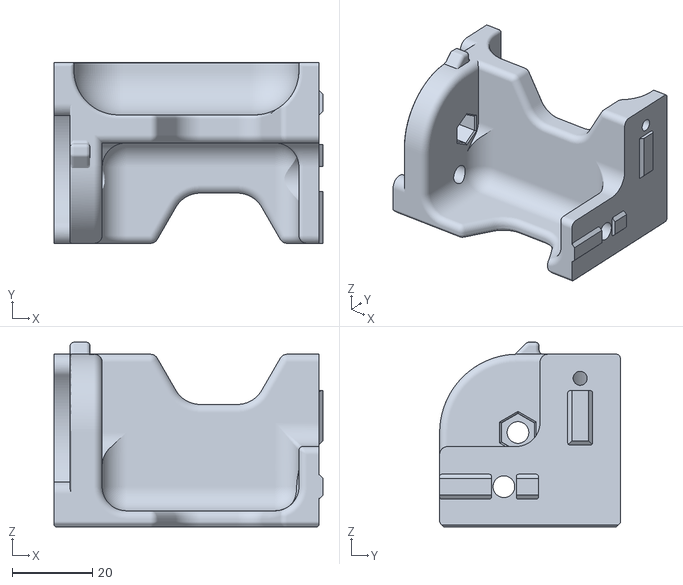
[picture p158: CAD file, 2022-12-02]
Mods/vt_lowered_Z_motor_mounts/STL/Corner_B-v1.1.stl
67.0 x 45.0 x 46.0
