Exerqtor/Voron/Mods/vt_wobblex_carriers/CAD/Rear Wobblex Carriers-MGN12H.step

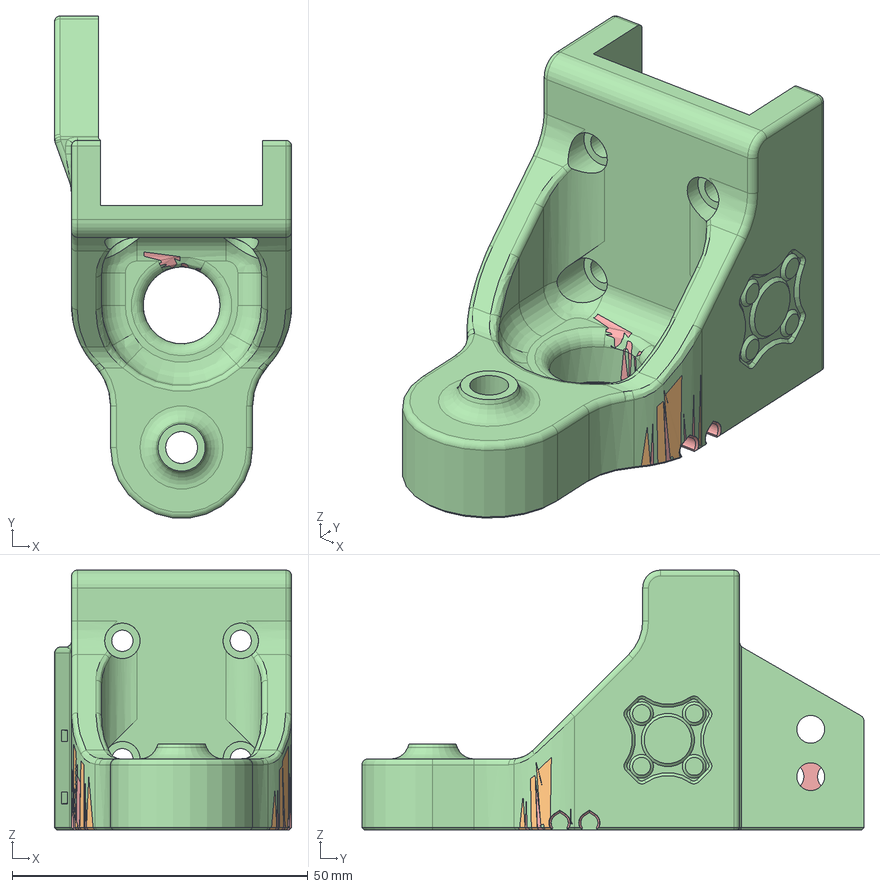
[picture p159: CAD file, 2023-08-06]
Mods/vt_wobblex_carriers/CAD/Rear Wobblex Carriers-MGN12H.step
40.1 x 84.8 x 43.9 mm
3.1mm
3.0mm
2.9mm
