Exerqtor/Voron/Mods/vt_wobblex_carriers/STL/rear_top_support.stl

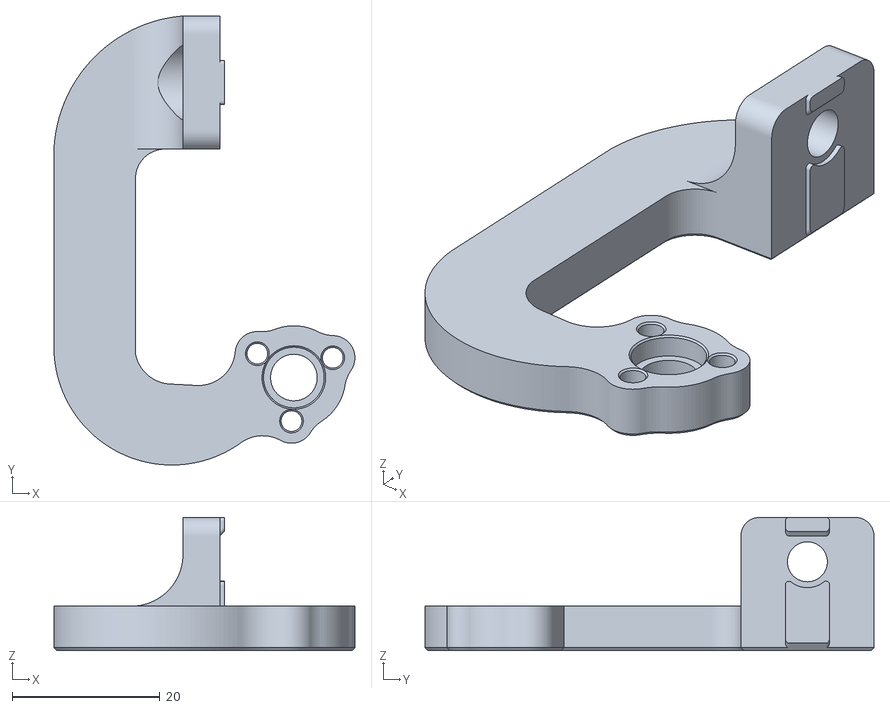
[picture p160: CAD file, 2023-08-07]
Mods/vt_wobblex_carriers/STL/rear_top_support.stl
40.7 x 60.7 x 18.0
