Exerqtor/Voron/Mods/canopy_ptfe_passthrough/STL/350.stl

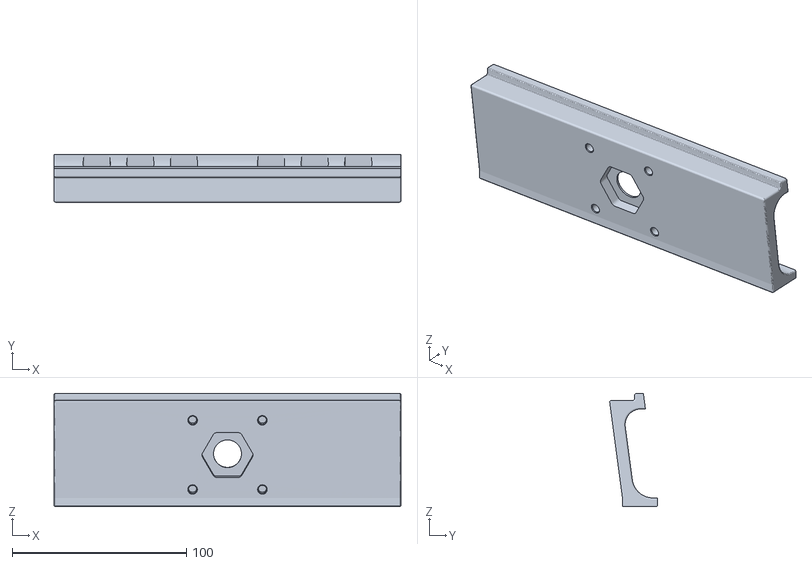
[picture p161: CAD file, 2024-03-30]
Mods/canopy_ptfe_passthrough/STL/350.stl
199.0 x 27.3 x 65.0
