Exerqtor/Voron/Mods/fume_pack/DXF/300mm.dxf

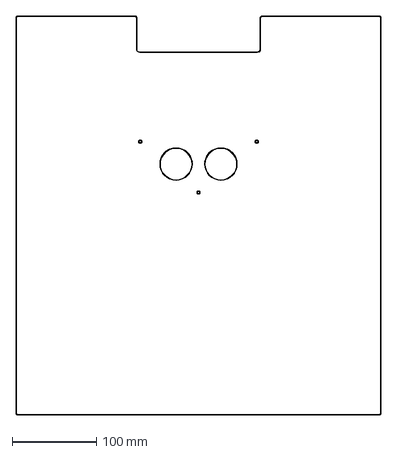
[picture p162: CAD file, 2023-06-20]
Mods/fume_pack/DXF/300mm.dxf
433.0 x 473.0 mm
