Exerqtor/Voron/Mods/fume_pack/DXFs/VT-350mm.dxf

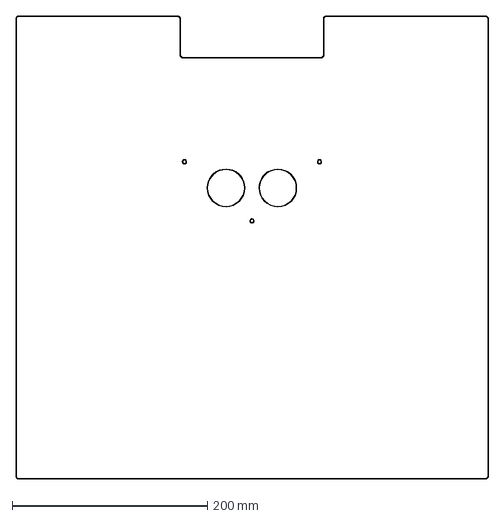
[picture p163: CAD file, 2023-06-24]
Mods/fume_pack/DXFs/VT-350mm.dxf
483.0 x 473.0 mm
