Exerqtor/Voron/Mods/fume_pack/STL/[a]_Lid-v1.1.stl

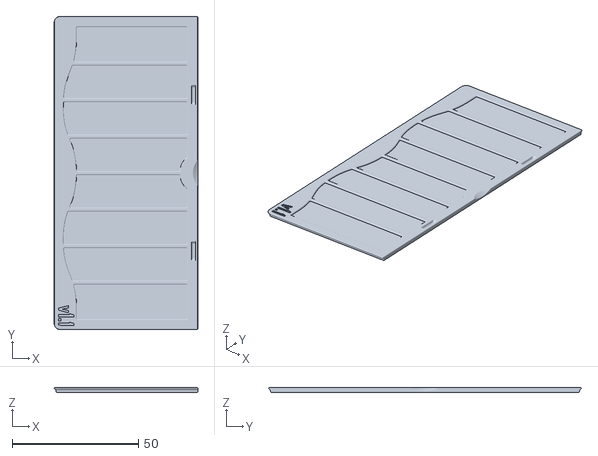
[picture p164: CAD file, 2022-12-01]
Mods/fume_pack/STL/[a]_Lid-v1.1.stl
56.8 x 123.9 x 1.78
