Exerqtor/Voron/Mods/mesh_skirts/Middle_Fan_Support/STL/fan_grill_b-mesh_x2.stl

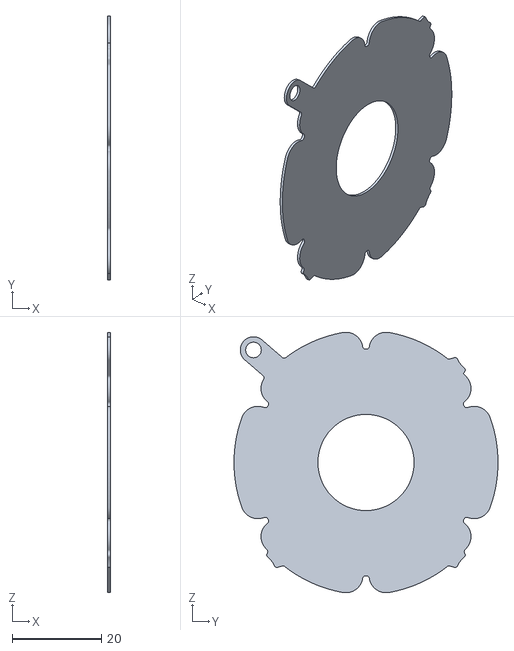
[picture p165: CAD file, 2023-04-12]
Mods/mesh_skirts/Middle_Fan_Support/STL/fan_grill_b-mesh_x2.stl
0.6 x 59.1 x 58.3
