Exerqtor/Voron/Mods/mesh_skirts/VT/STL/250/side_skirt_b_250_x2.stl

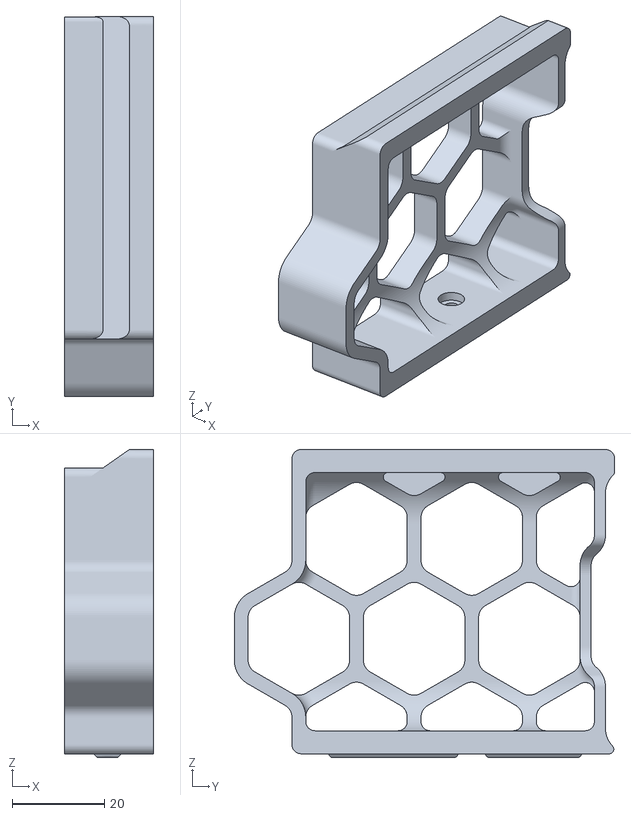
[picture p166: CAD file, 2023-04-16]
Mods/mesh_skirts/VT/STL/250/side_skirt_b_250_x2.stl
19.4 x 82.5 x 66.8
