Exerqtor/Voron/Mods/mesh_skirts/VT/STL/300/[a]_front_skirt_a_300-mesh.stl

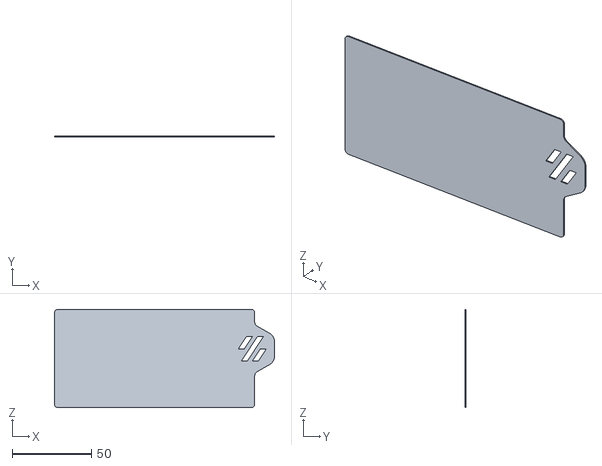
[picture p167: CAD file, 2023-04-16]
Mods/mesh_skirts/VT/STL/300/[a]_front_skirt_a_300-mesh.stl
139.0 x 0.6 x 62.0
