Exerqtor/Voron/Mods/mesh_skirts/VT/STL/350/[a]_rear_center_skirt_350-mesh.stl

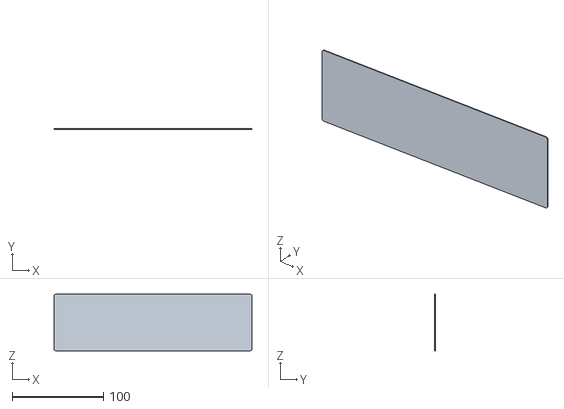
[picture p168: CAD file, 2023-04-16]
Mods/mesh_skirts/VT/STL/350/[a]_rear_center_skirt_350-mesh.stl
217.0 x 0.6 x 62.0
