Exerqtor/Voron/Mods/mesh_skirts/VT/STL/[a]_power_inlet_adamstech.stl

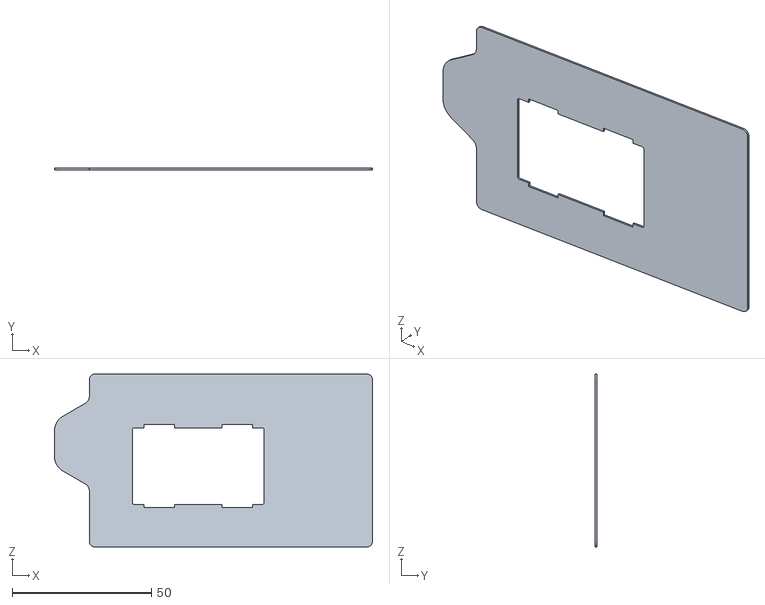
[picture p169: CAD file, 2023-04-22]
Mods/mesh_skirts/VT/STL/[a]_power_inlet_adamstech.stl
114.0 x 0.6 x 62.0
