Exerqtor/Voron/Mods/pepe_pack_v2/STL/[a]_Cartridge_lid-v2.2.stl

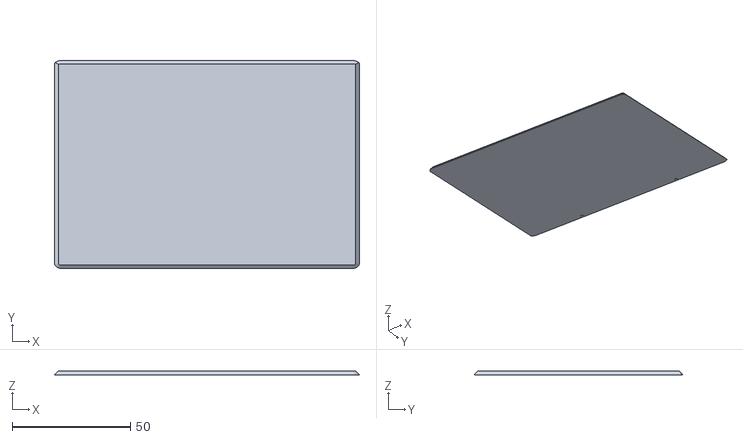
[picture p170: CAD file, 2022-11-28]
Mods/pepe_pack_v2/STL/[a]_Cartridge_lid-v2.2.stl
129.0 x 87.9 x 1.80
