Exerqtor/Voron/Mods/revo_nozzle_storage_skirt/STL/VT/350/B/MM-revo_nozzle_side_skirt_b_350-lid.stl

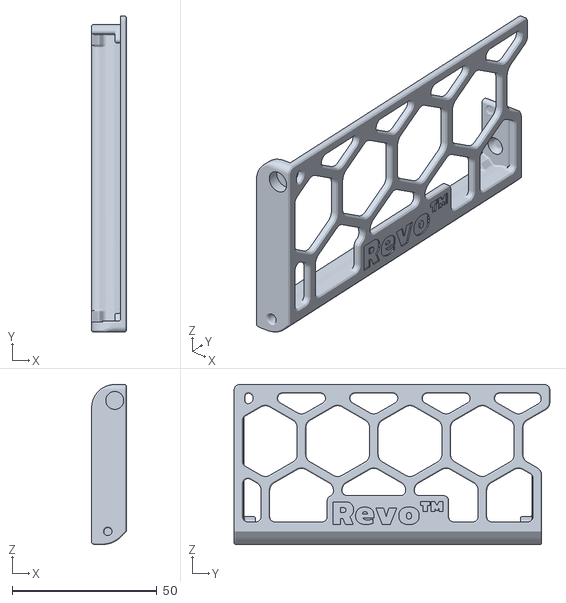
[picture p171: CAD file, 2023-06-25]
Mods/revo_nozzle_storage_skirt/STL/VT/350/B/MM-revo_nozzle_side_skirt_b_350-lid.stl
12.0 x 109.1 x 55.3
