Exerqtor/Voron/Mods/service_rockers/STL/brace_right.stl

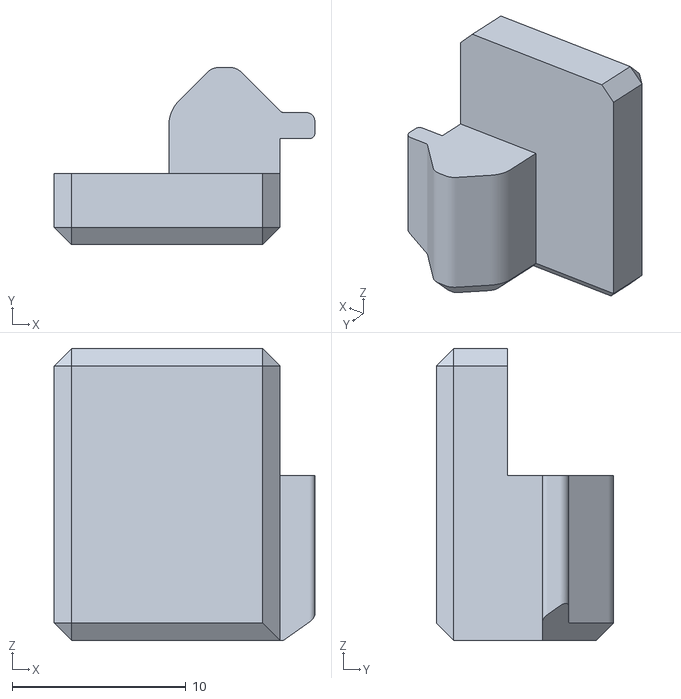
[picture p172: CAD file, 2023-04-29]
Mods/service_rockers/STL/brace_right.stl
15.0 x 10.2 x 16.8
