Exerqtor/Voron/Mods/stealthburner_cw2_style_lgx_lite_mount/STL/spacer_x2.stl

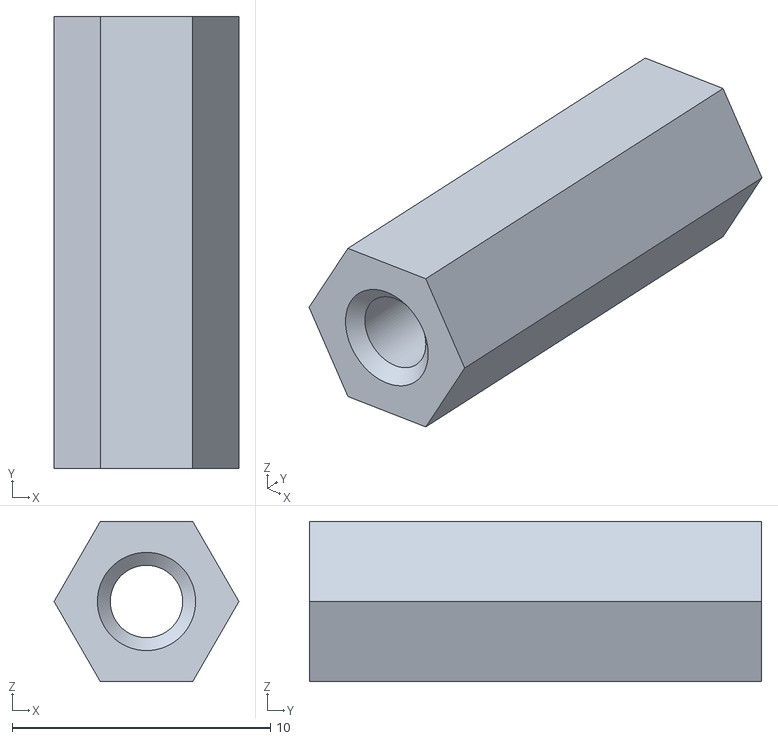
[picture p173: CAD file, 2022-08-07]
Mods/stealthburner_cw2_style_lgx_lite_mount/STL/spacer_x2.stl
7.16 x 17.5 x 6.20
