Exerqtor/Voron/Mods/trident_ptfe_guides/STL/R50-90°.stl

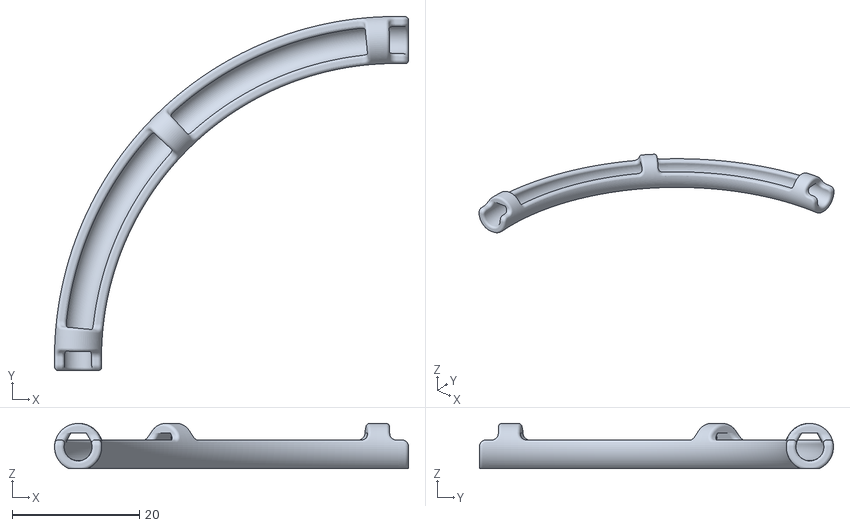
[picture p174: CAD file, 2022-11-30]
Mods/trident_ptfe_guides/STL/R50-90°.stl
55.7 x 55.7 x 7.10
