Exerqtor/Voron/Mods/vt_lowered_Z_motor_mounts/STL/[a]_Cover_x3-v1.1.stl

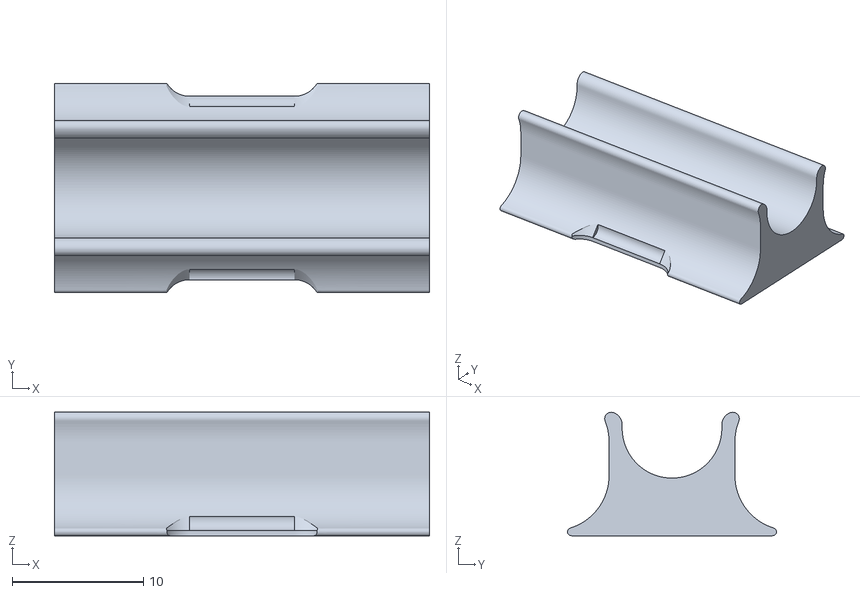
[picture p175: CAD file, 2022-12-02]
Mods/vt_lowered_Z_motor_mounts/STL/[a]_Cover_x3-v1.1.stl
28.6 x 15.9 x 9.42
