Exerqtor/Voron/Mods/vt_wobblex_carriers/CAD/Pin clearance test.step

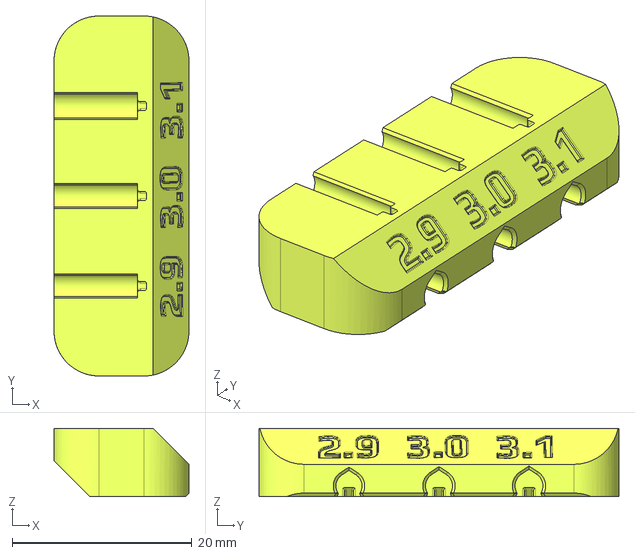
[picture p176: CAD file, 2023-04-26]
Mods/vt_wobblex_carriers/CAD/Pin clearance test.step
15.0 x 40.0 x 7.60 mm
