Exerqtor/Voron/Mods/vt_wobblex_carriers/STL/front_left_top_support.stl

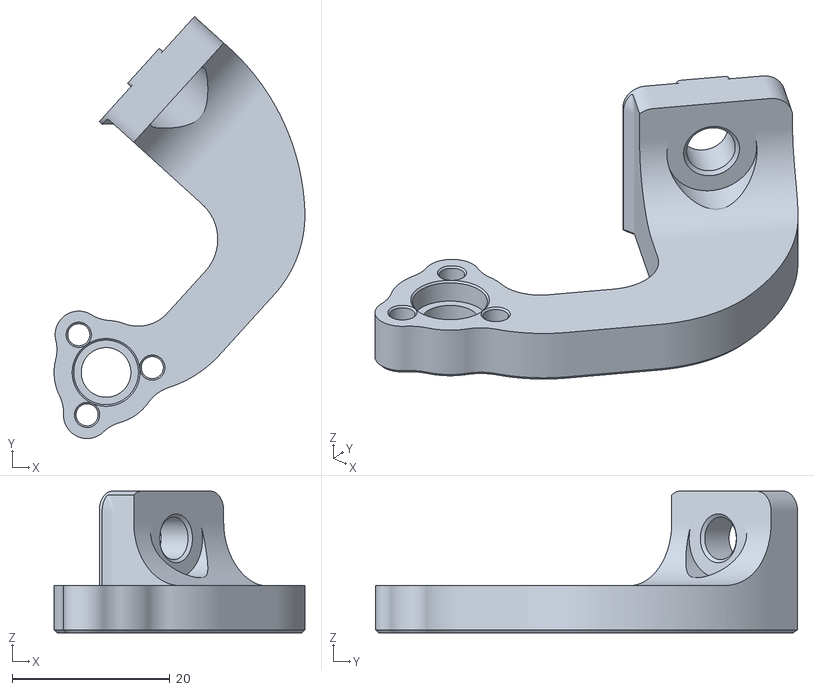
[picture p177: CAD file, 2023-08-07]
Mods/vt_wobblex_carriers/STL/front_left_top_support.stl
31.8 x 53.5 x 18.0
