Exerqtor/Voron/Mods/canopy_ptfe_passthrough/STL/300.stl

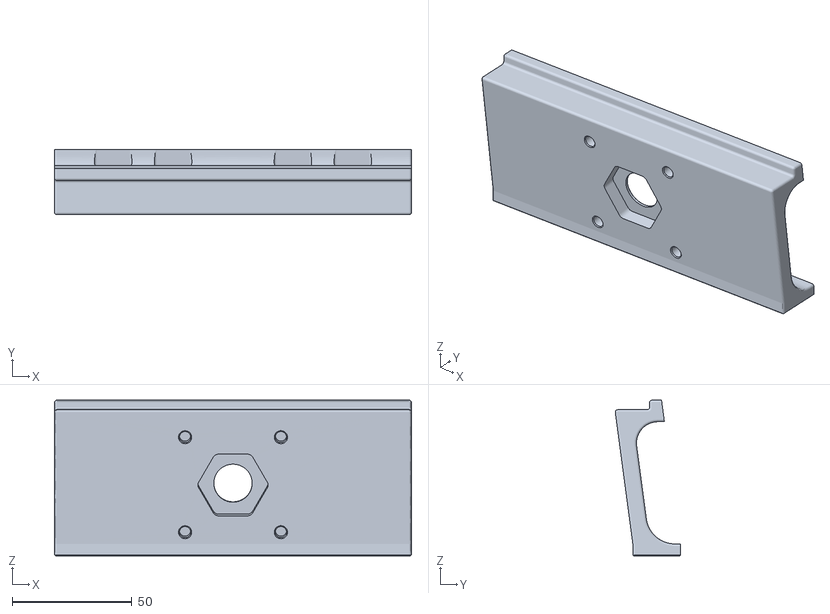
[picture p178: CAD file, 2024-03-30]
Mods/canopy_ptfe_passthrough/STL/300.stl
149.0 x 27.3 x 65.0
