Exerqtor/Voron/Mods/fume_pack/DXF/350mm.dxf

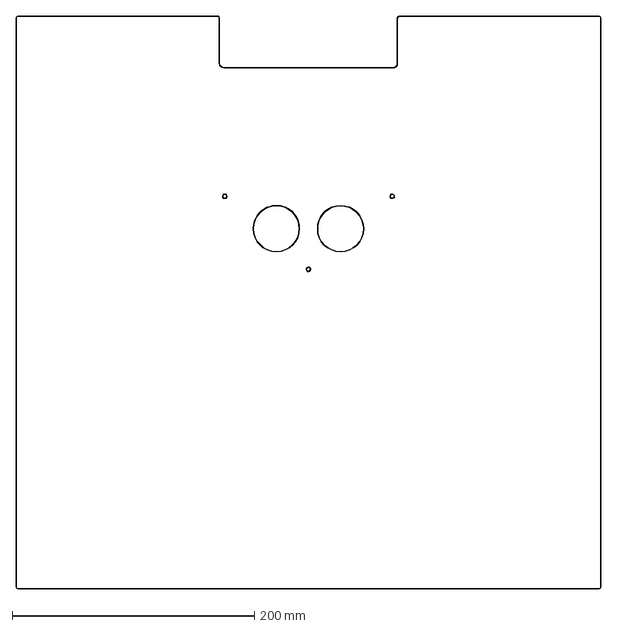
[picture p179: CAD file, 2023-06-20]
Mods/fume_pack/DXF/350mm.dxf
483.0 x 473.0 mm
