Exerqtor/Voron/Mods/fume_pack/DXFs/V2-350mm.dxf

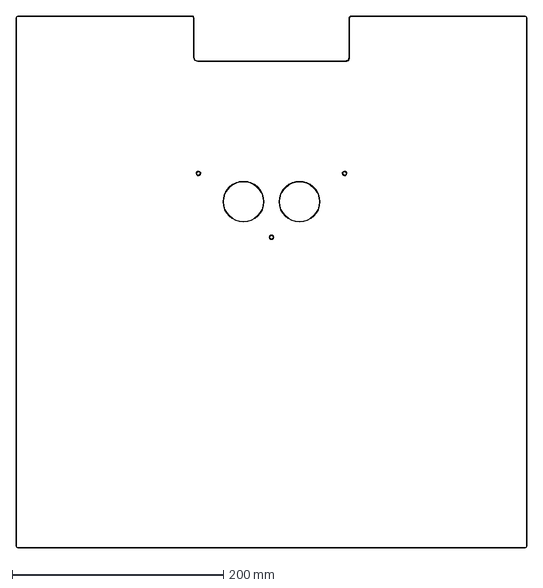
[picture p180: CAD file, 2023-06-24]
Mods/fume_pack/DXFs/V2-350mm.dxf
483.0 x 503.0 mm
