Exerqtor/Voron/Mods/mesh_skirts/Middle_Fan_Support/STL/[a]_side_fan_support-mesh_x2.stl

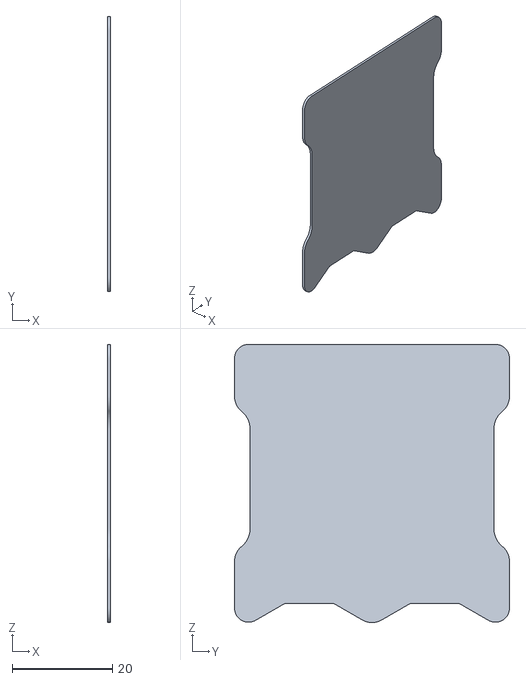
[picture p181: CAD file, 2023-04-12]
Mods/mesh_skirts/Middle_Fan_Support/STL/[a]_side_fan_support-mesh_x2.stl
0.6 x 54.8 x 55.4
