Exerqtor/Voron/Mods/mesh_skirts/V2/STL/front_center_logo.stl

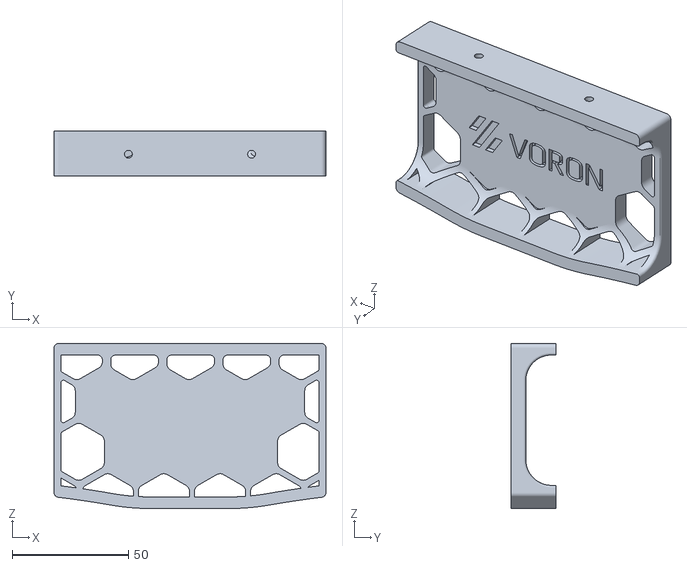
[picture p182: CAD file, 2023-04-13]
Mods/mesh_skirts/V2/STL/front_center_logo.stl
117.0 x 19.4 x 71.0
