Exerqtor/Voron/Mods/mesh_skirts/VT/STL/250/[a]_front_skirt_a_250-mesh.stl

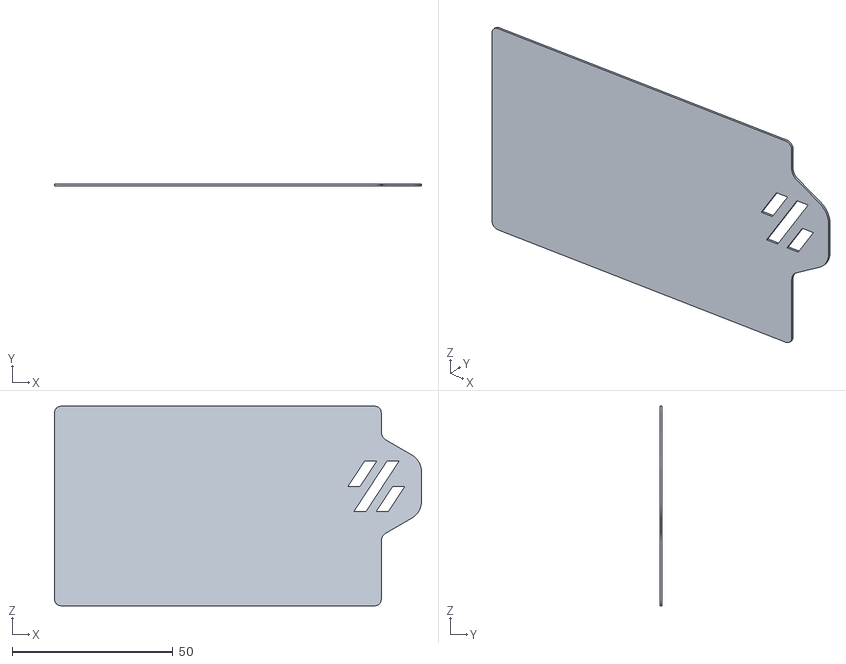
[picture p183: CAD file, 2023-04-16]
Mods/mesh_skirts/VT/STL/250/[a]_front_skirt_a_250-mesh.stl
114.0 x 0.6 x 62.0
