Exerqtor/Voron/Mods/mesh_skirts/VT/STL/300/rear_center_skirt_300.stl

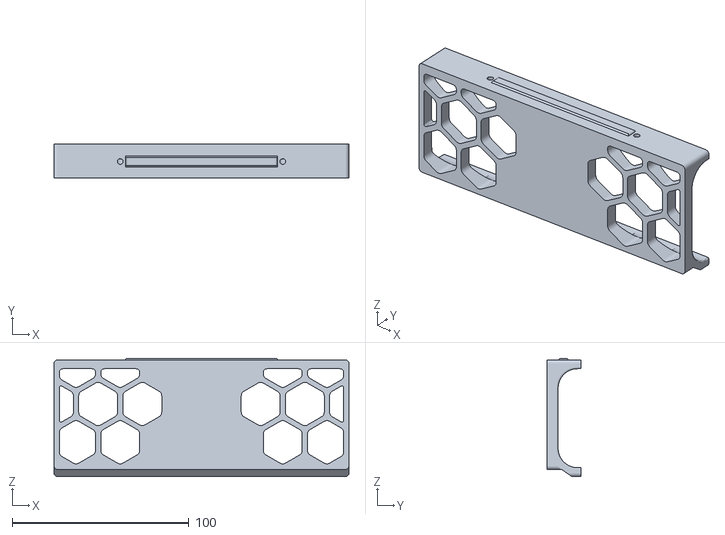
[picture p184: CAD file, 2023-04-16]
Mods/mesh_skirts/VT/STL/300/rear_center_skirt_300.stl
167.0 x 19.4 x 66.8
