Exerqtor/Voron/Mods/mesh_skirts/VT/STL/keystone_panel.stl

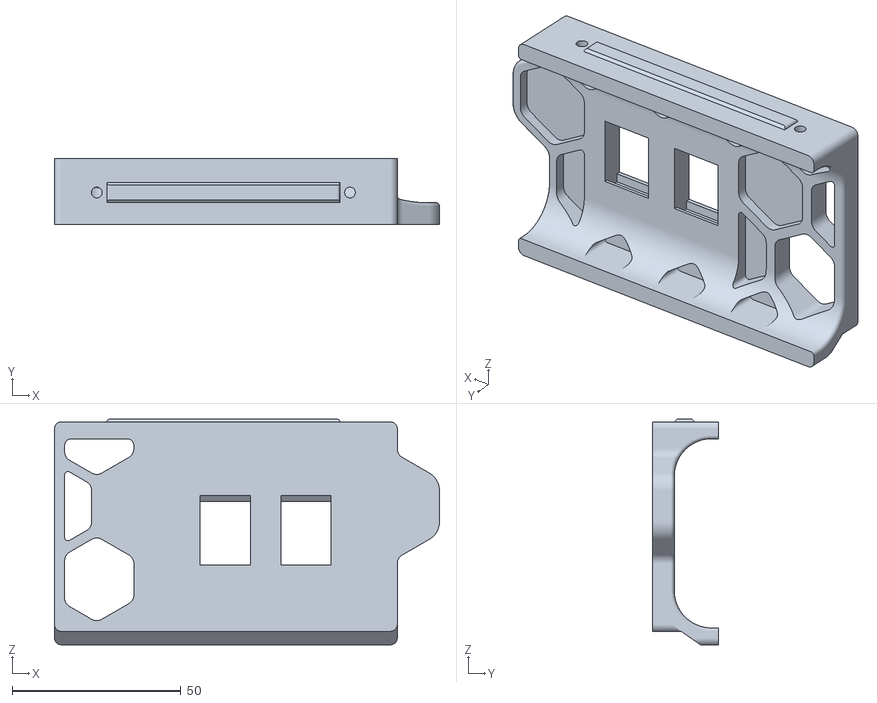
[picture p185: CAD file, 2023-04-16]
Mods/mesh_skirts/VT/STL/keystone_panel.stl
114.0 x 19.4 x 66.8
