Exerqtor/Voron/Mods/pepe_pack_v2/STL/[TPU]_Fan_gasket_x2-v2.2.stl

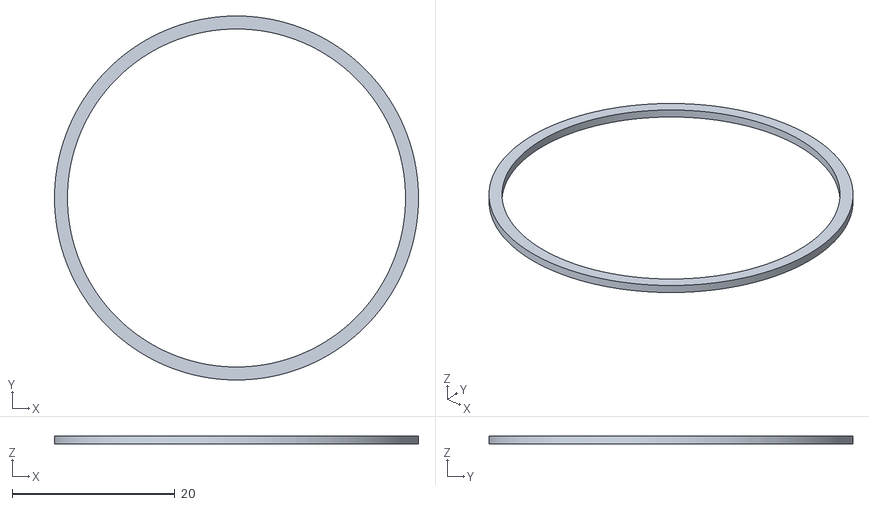
[picture p186: CAD file, 2022-11-28]
Mods/pepe_pack_v2/STL/[TPU]_Fan_gasket_x2-v2.2.stl
44.8 x 44.8 x 1.00
