Exerqtor/Voron/Mods/stealthburner_cw2_style_lgx_lite_mount/STL/lgx_lite_chainmount_3-hole_low_profile.stl

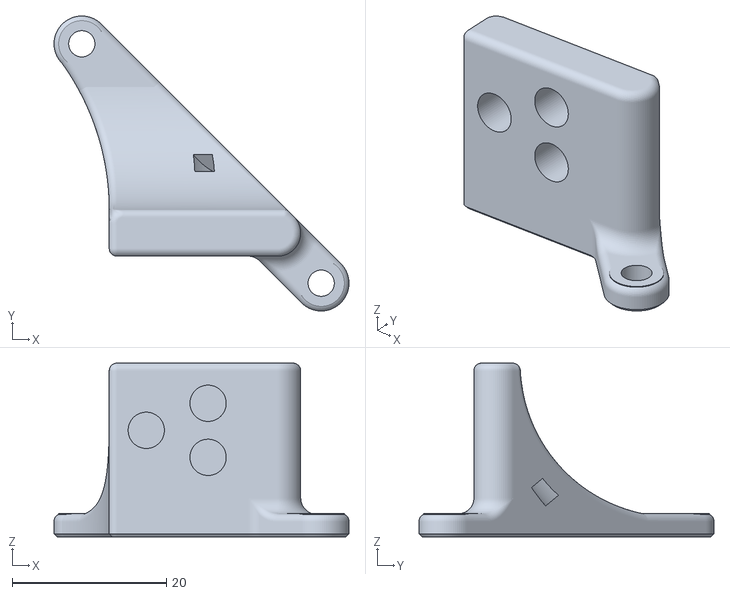
[picture p188: CAD file, 2022-08-07]
Mods/stealthburner_cw2_style_lgx_lite_mount/STL/lgx_lite_chainmount_3-hole_low_profile.stl
38.2 x 38.2 x 22.5
