Exerqtor/Voron/Mods/trident_ptfe_support-v2/STL/Arm-plain.stl

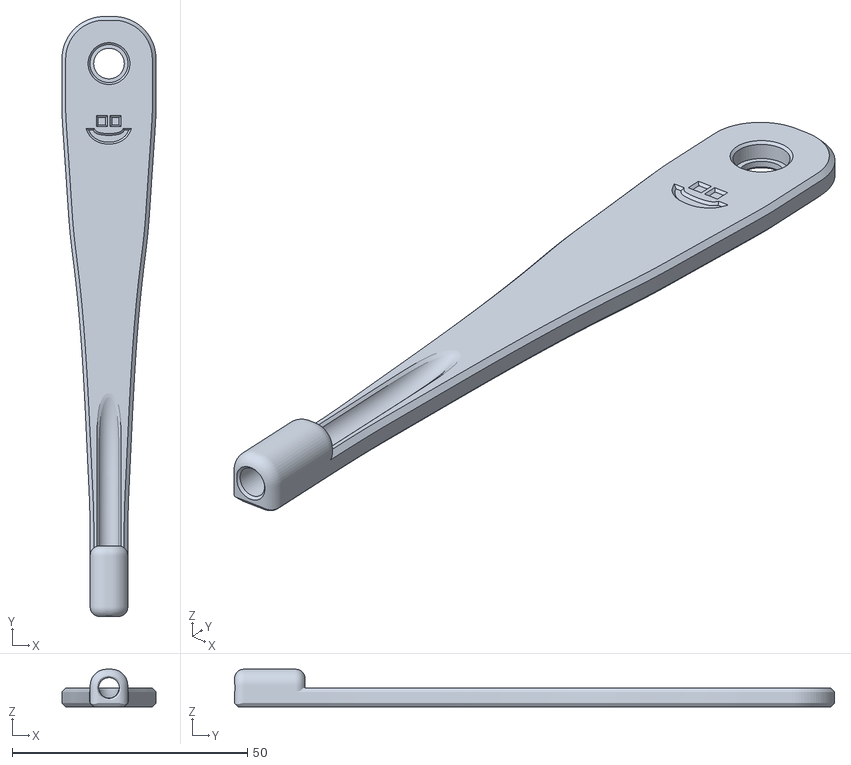
[picture p189: CAD file, 2022-11-29]
Mods/trident_ptfe_support-v2/STL/Arm-plain.stl
20.0 x 127.5 x 8.00
