Exerqtor/Voron/Mods/canopy_ptfe_passthrough/STL/Cover_plate.stl

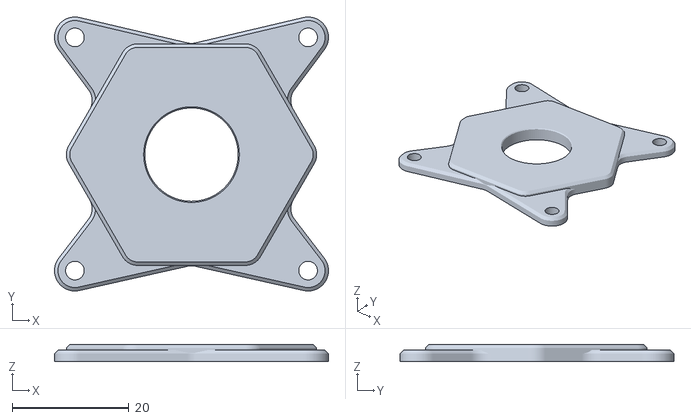
[picture p190: CAD file, 2024-03-30]
Mods/canopy_ptfe_passthrough/STL/Cover_plate.stl
47.0 x 47.0 x 3.00
