Exerqtor/Voron/Mods/fume_pack/DXFs/VT-300mm.dxf

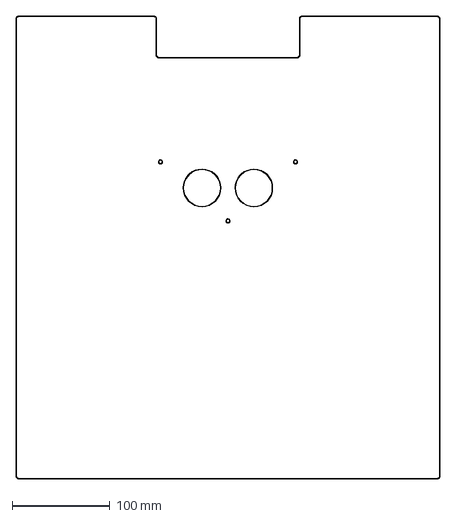
[picture p191: CAD file, 2023-06-24]
Mods/fume_pack/DXFs/VT-300mm.dxf
433.0 x 473.0 mm
