Exerqtor/Voron/Mods/mesh_skirts/V2/STL/belt_guard_a-mesh_x2.stl

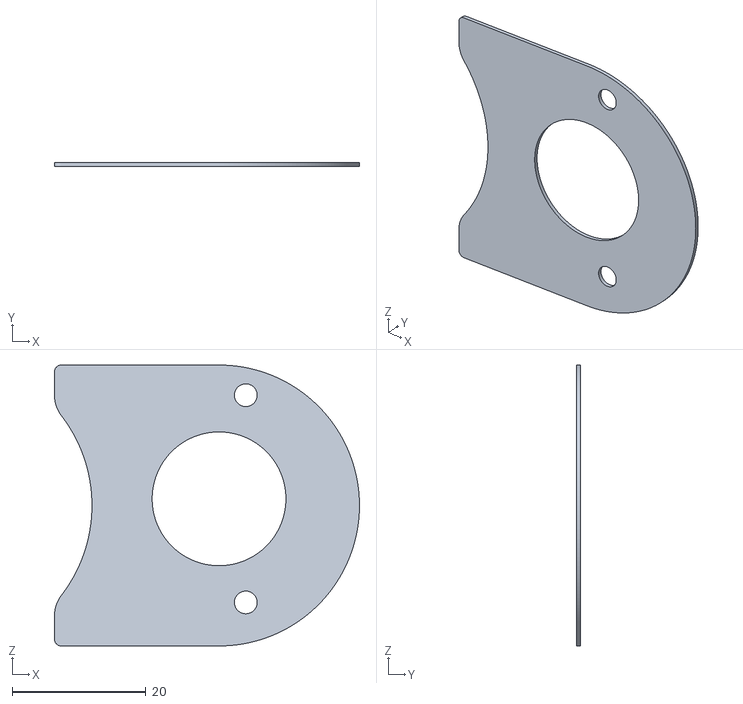
[picture p192: CAD file, 2023-04-13]
Mods/mesh_skirts/V2/STL/belt_guard_a-mesh_x2.stl
45.6 x 0.6 x 42.0
