Exerqtor/Voron/Mods/mesh_skirts/VT/STL/250/[a]_side_skirt_a_250-mesh_x2.stl

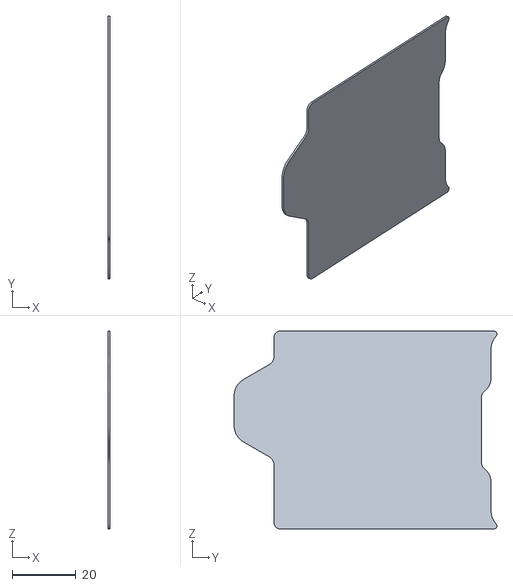
[picture p193: CAD file, 2023-04-16]
Mods/mesh_skirts/VT/STL/250/[a]_side_skirt_a_250-mesh_x2.stl
0.6 x 82.3 x 62.0
