Exerqtor/Voron/Mods/mesh_skirts/VT/STL/300/front_skirt_a_300.stl

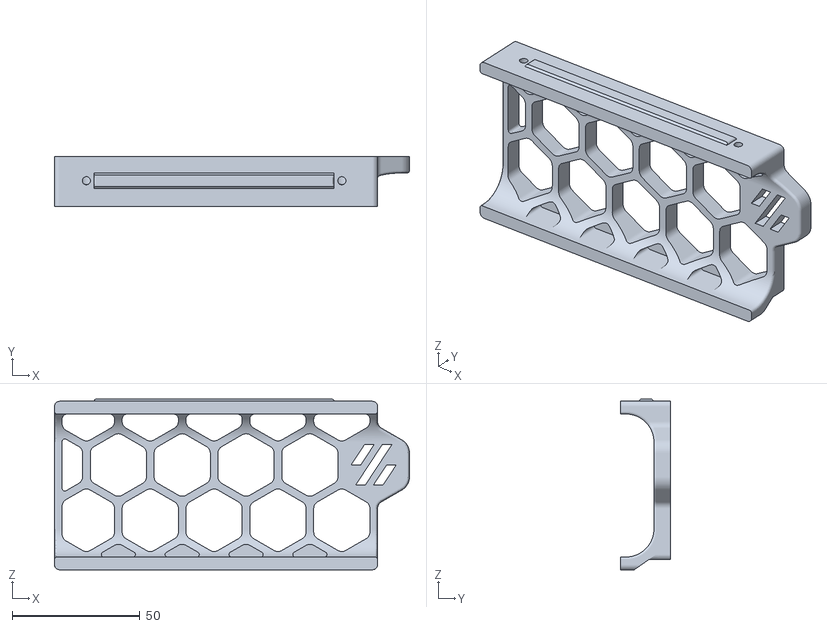
[picture p194: CAD file, 2023-04-16]
Mods/mesh_skirts/VT/STL/300/front_skirt_a_300.stl
139.0 x 19.4 x 66.8
