Exerqtor/Voron/Mods/mesh_skirts/VT/STL/350/[a]_front_skirt_a_350-mesh.stl

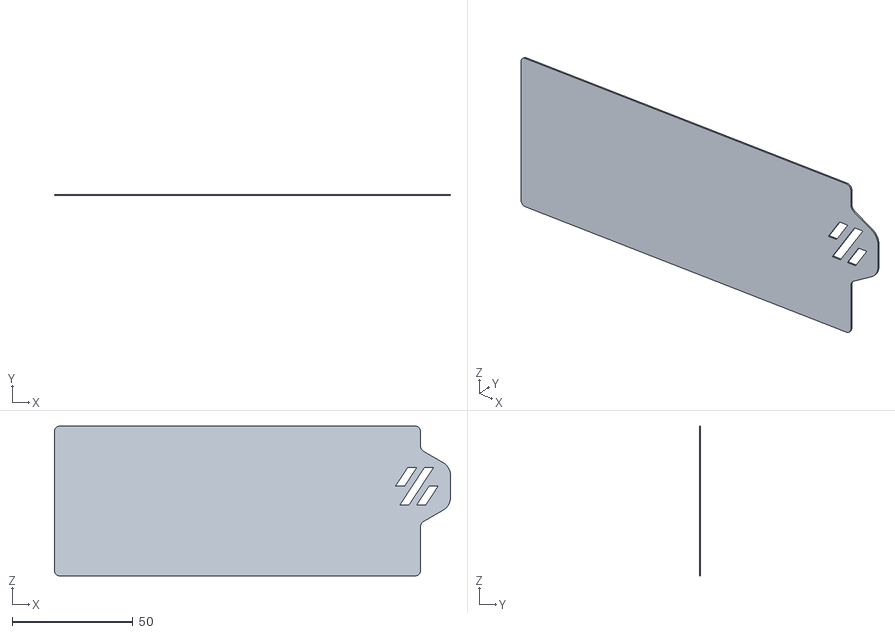
[picture p195: CAD file, 2023-04-16]
Mods/mesh_skirts/VT/STL/350/[a]_front_skirt_a_350-mesh.stl
164.0 x 0.6 x 62.0
