Exerqtor/Voron/Mods/mesh_skirts/VT/STL/[a]_power_inlet_filtered-mesh.stl

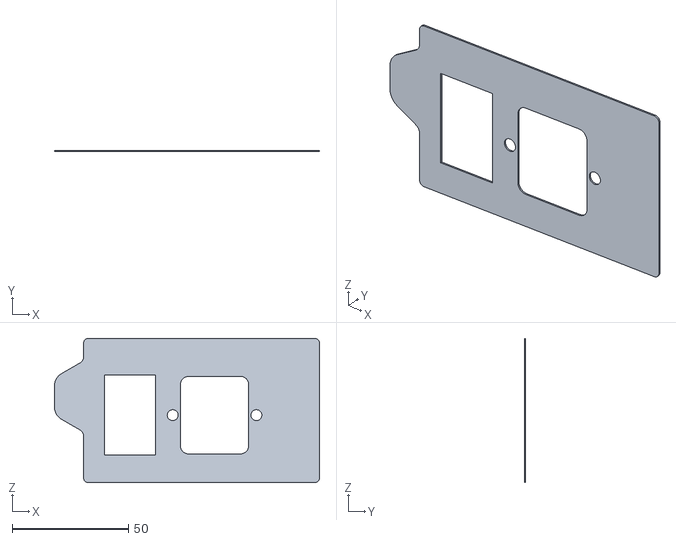
[picture p196: CAD file, 2023-04-16]
Mods/mesh_skirts/VT/STL/[a]_power_inlet_filtered-mesh.stl
114.0 x 0.6 x 62.0
