Exerqtor/Voron/Mods/trident_ptfe_support-v2/STL/Mount.stl

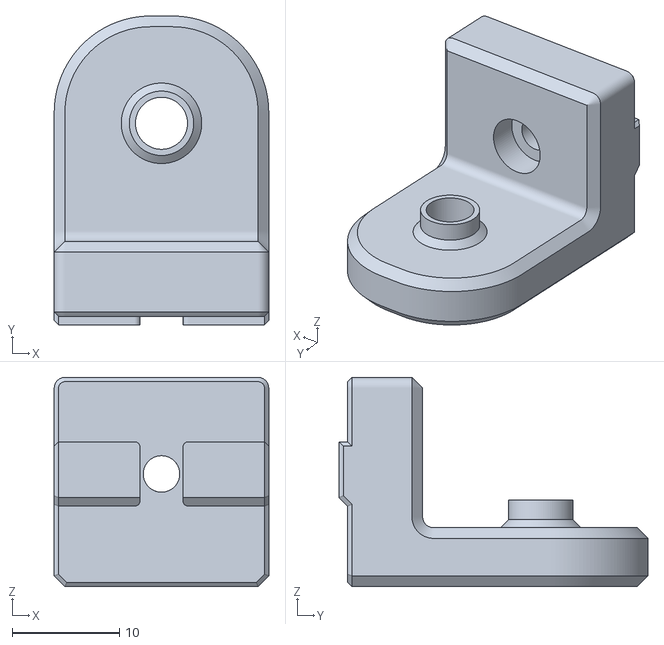
[picture p197: CAD file, 2022-11-29]
Mods/trident_ptfe_support-v2/STL/Mount.stl
20.0 x 28.8 x 19.5
