Exerqtor/Voron/Mods/vt_lowered_Z_motor_mounts/STL/Z_Motor_Mount_Rear-v1.1.stl

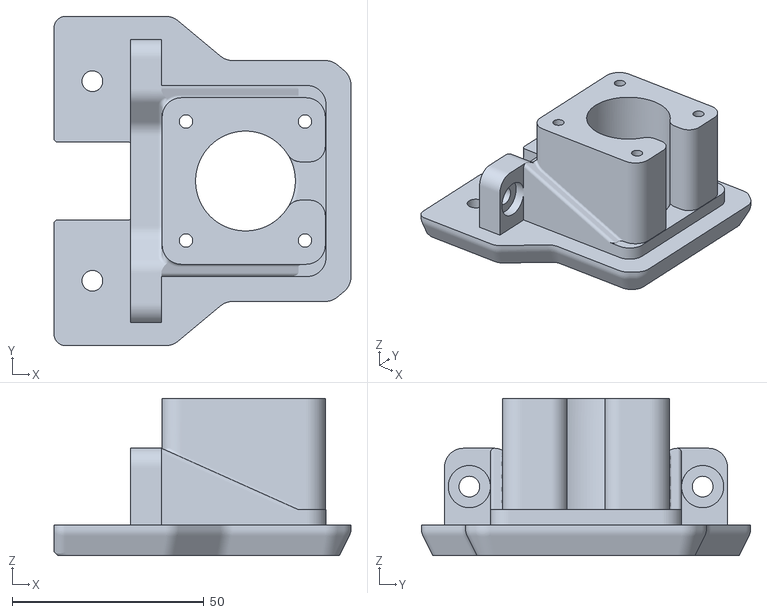
[picture p198: CAD file, 2022-12-02]
Mods/vt_lowered_Z_motor_mounts/STL/Z_Motor_Mount_Rear-v1.1.stl
77.4 x 85.8 x 41.0
