Exerqtor/Voron/Mods/vt_wobblex_carriers/STL/2.9mm/WobbleX_2.9mm-MGN9H_Z_Carriage_Rear_3-hole-(Generic).stl

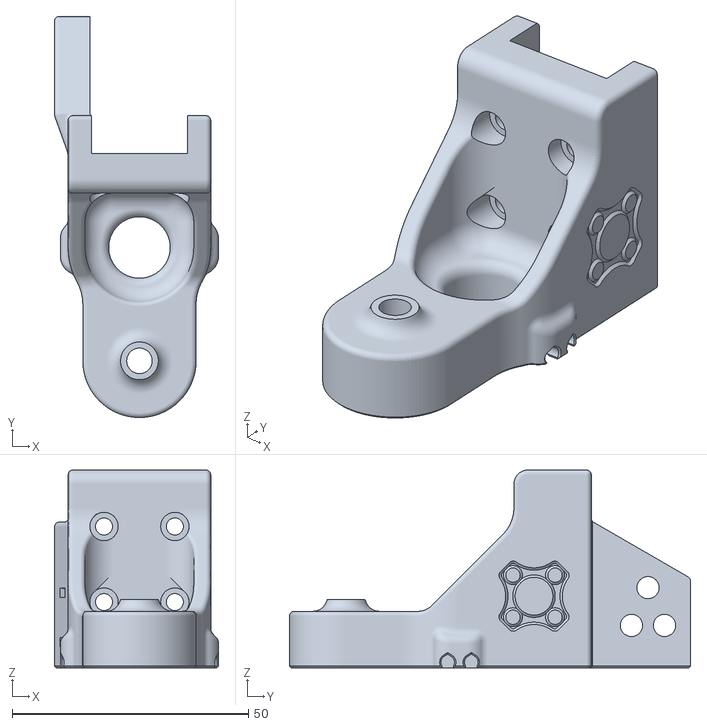
[picture p199: CAD file, 2023-08-06]
Mods/vt_wobblex_carriers/STL/2.9mm/WobbleX_2.9mm-MGN9H_Z_Carriage_Rear_3-hole-(Generic).stl
34.8 x 84.9 x 41.9
