Exerqtor/Voron/Mods/fume_pack/changelog/v1.2.1/README.md

# fume pack

## CHANGELOG v1.2.1
- 04.12.2022: I had to add little feature on the outside of the main bodies to compensate for the lost wall thickness introduced due to the detachable backplate in [v1.2](https://github.com/Exerqtor/Voron/tree/main/Mods/fume_pack/changelog/v1.2).
###### Pictures:
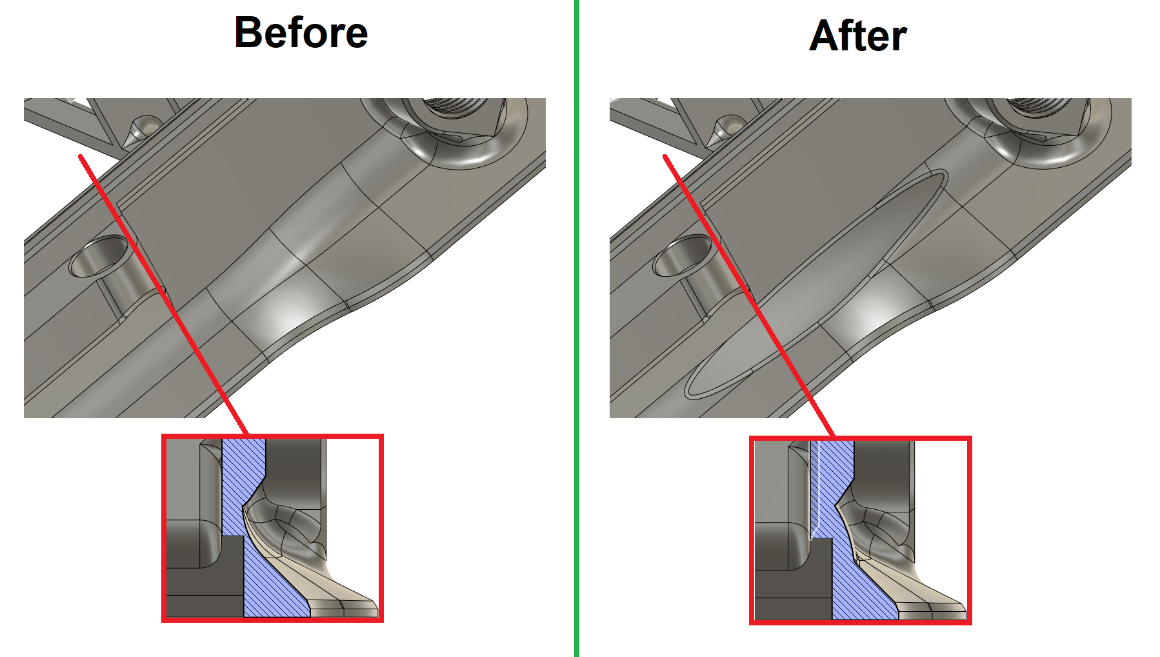
[picture p203: Mods/fume_pack/changelog/v1.2.1/1.png]
